mickecamino/RT-datorn/Gamla RT-datorn/CÅ-8001/README-EN.md

# CA-8001 ACIA with 2 serial ports
Apdated schematic för CÅ-8001 - the ones in the magazine and in the book are unfortunately incorrect.
