mickecamino/RT-datorn/Program från MPU-laren/1982 - 1/README.md

# Program från MPU-laren #1-1982	
```
CLOCKSET.ASM - Program som sätter tiden på en MSM5832
DIR.ASM      - Bra version av DIR som visar mer än standard DIR
FLEXPAT.ASM  - Patch för FLEX 2.65 läs av MSM5832 klocka
UNDEL.ASM    - Återskapar raderade filer
VOXMEM.ASM   - Program som talar - kräver VS-1 Speaker Board
VOXMEM1.ASM  - Program som talar - kräver VS-1 Speaker Board - alternativ röst
```
