mickecamino/RT-datorn/Gamla RT-datorn/CÅ-8010/README-EN.md

# CA-8010 EPROM-programmer
EPROM-programmer for RT-computer  
A programmer that programs 2708, 2716 with three different voltages, 2716/2516 with single voltage and 2532/2732.

## Files
* CPROG.CMD  -  CÅ-Elektronik Epromprogrammer Cprog 1.0 for 6809
* TPROG.CMD  -  CÅ-Elektronik Epromprogrammer Tprog 1.0 for 6808
* CÅ-8010 manual.pdf - Manual for the programmer
