mickecamino/RT-datorn/Gamla RT-datorn/CÅ-6819/README-EN.md

# CA-6819 CPU board
CPU board with two processorns, 6800 and 6809, selectable with a switch.  

Monitors:
6800 - TBUG 2C
```
TBUG-2C-E400.bin
TBUG-2C-EC00.bin
```
6809 - CBUG 2.3
```
CBUG-2.3-F800.bin
CBUG-2.3-FC00.bin
```
