mickecamino/RT-datorn/Nya RT-datorn/RT-Backplane/README-EN.md

# Backplane for RT-datorn.
A backplane for RT-datorn with 8 slots and a Phoenix-plug for power and connector for External Reset.
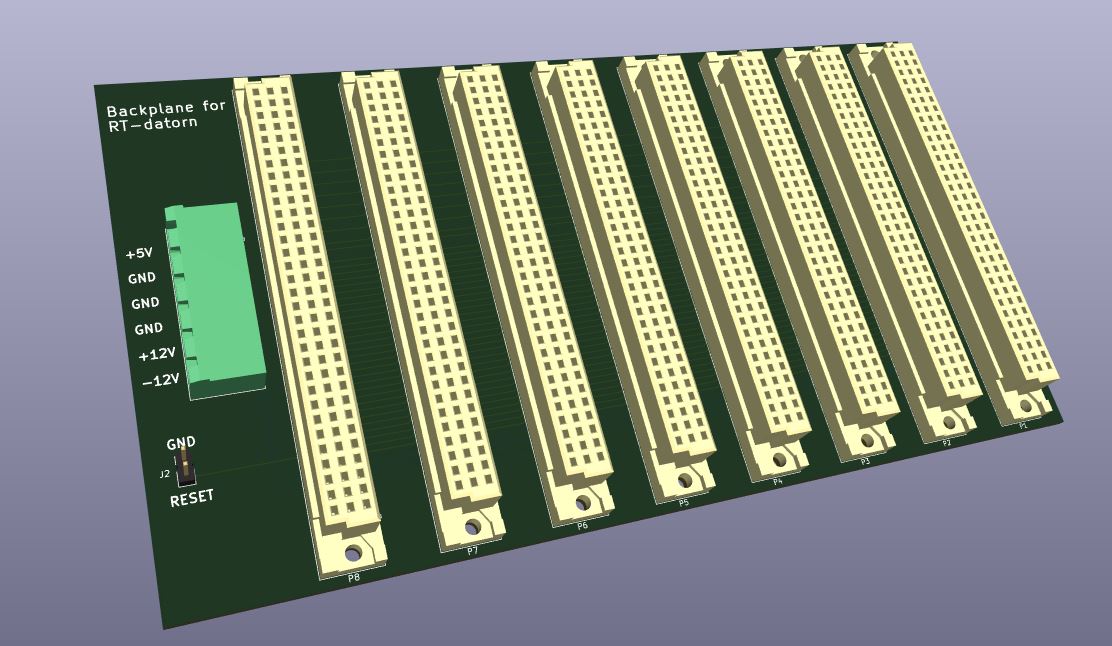
[picture p1: Nya RT-datorn/RT-Backplane/RT-backplane.jpg]
RT-Backplane
