mickecamino/RT-datorn/Nya RT-datorn/RT-Backplane/README.md

# Bakplan för RT-datorn.
Ett backplan för RT-datorn med 8 slottar och en Phoenix-plug för spänningsmatning samt uttag för External Reset.
RT-Backplane
