mickecamino/RT-datorn/Gamla RT-datorn/CÅ-800/README-EN.md

# CA-800 Motherboard
The first version of the motherboard, repalced with CA-801.  
The difference is that the power supply parts are moved off the motherboard and some component changes were made.
