mickecamino/RT-datorn/Gamla RT-datorn/CÅ-8014/README-EN.md

# CA-8014 Centronics printer output
Peripheral board with Centronics output for connecting parallel printers.  
No documentation or schematic found.
