mickecamino/RT-datorn/Gamla RT-datorn/CÅ-8015/README-EN.md

## CA-8015 - Real Time Clock
This peripheral board, with MSM5832, is a newer Real time Clock than CA-8005.  
The clock chip is a "real" real time clock used for computers with proper address and data ports.
