mickecamino/RT-datorn/Gamla RT-datorn/CÅ-8016/README-EN.md

# CA-8016 - Sound Effect board with SN76477
This peripheral board was probably never made due to low interest accoring to an article in the member magazine MPU-laren.  
It was listed in an old price list from Telko.
