mickecamino/RT-datorn/Gamla RT-datorn/CÅ-8017/README-EN.md

# CA-8017 - Floppy Controller
Peripheral board for connecting up to four single or double sided floppy drives, single density only.  
The peripheral board exists in two versions, CA-8017 and CA-8017B. The B variant fully supports double sided floppy drives
.
