mickecamino/RT-datorn/Gamla RT-datorn/CÅ-8018/README-EN.md

# CA-8018 - IEEE-488-bus connection
A special peripheral board for connecting IEEE-488 units.  
Also called HP-IP or GBIP. Used for controlling and reading instruments.
