mickecamino/RT-datorn/Gamla RT-datorn/CÅ-8020/README-EN.md

# CA-8020 - DEBUG board
For debugging the RT-computer.  
No documentation or schematic found.
