mickecamino/RT-datorn/Gamla RT-datorn/CÅ-8025/README-EN.md

# CA-8025 - EPROM board
EPROM board for 8 pcs. 2K 2516 EPROMS. Up to three cards can be used in the RT-computer.
