mickecamino/RT-datorn/Gamla RT-datorn/CÅ-8027/README-EN.md

## CA-8027 - Arithmetic Processing Unit
This board with AM9511 havean Arithmetic Processing Unit (APU) device that provides high performance fixed and floating point arithmetic and a variety of floating point
trigonometric and mathematical operations, 16 and 32 bits fixed point operations and 32 bits floating point operations.  

No program examples found for this board.
