mickecamino/RT-datorn/Gamla RT-datorn/CÅ-8030/README-EN.md

## CA-8030 - Unknown function
This board was donated by Åke Holm. No silk screen or documantation exists.  
The only bus connection used are +5v, +12v, -12v, R/W, D0, RESET, A0, A1 and GND
