mickecamino/RT-datorn/Gamla RT-datorn/CÅ-8034/README-EN.md

## CA-8034 - Unknown function
This board was donated by Åke Holm. No silk screen or documentation exists.  
The board uses all bus connectors and has a 12-pin connector at the top.  
The board seems to be using one 74LS138 and two 6821 PIA
