mickecamino/RT-datorn/Gamla RT-datorn/CÅ-8091/README-EN.md

# CA-8091 - Lab board with PIA
Lab board with 6821 PIA.
