mickecamino/RT-datorn/Gamla RT-datorn/CÅ-8092/README-EN.md

# CA-8092 - Lab board ACIA/SSDA/ADLC
Lab board with ACIA (Asynchronous Communications Interface Adapter), SSDA (Synchronous Serial Data Adapter) and ADLC (Advanced Data Link Controller)
