mickecamino/RT-datorn/Gamla RT-datorn/CÅ-8095/README-EN.md

# CA-8095 - Riser board for the 22-pin bus
A riser board for the 22-pin peripheral bus. Used for testing and fault finding on peripheral cards.
