mickecamino/RT-datorn/Gamla RT-datorn/CÅ-9000/README-EN.md

# CA-9000 - Riser board for the CPU-card
A riser board for the CPU card. Used for test and fault finding.
