mickecamino/RT-datorn/Nya RT-datorn/CÅ-813/README-EN.md

# CÅ-813 I/O board with RTC	
The new board for serial communication is called CÅ-813 and it replaces the older boards 8001, 8014 and 8015.  
It features a programmable serial communication IC for V24, a printer connection with parallel interface (Centronics) and a Real Time Clock (MSM5832) with battery backup.  
The connection for printer and serial is via a 60-pin connector. 36 pins for the printer and 24 for the serial interface.  
At least two releases were made:
CÅ-813, first release with an INS2651 as ACIA.  
CÅ-813A, second release with a 6551 as ACIA.  

See also CÅ-833
