mickecamino/RT-datorn/Nya RT-datorn/CÅ-816/README-EN.md

# CÅ-816 - EPROM board
The new EPROM-board is called 816 and has 16 EPROM-sockets for 2532 EPROM's, each EPROM contains 4 kb. A total of 64 kb permanent memory is possible.. 
The board can hold for, example, the operating system FLEX and a BASIC interpreter. The addressing of the EPROM board is done via one single address. With a small software routine, loading from the boards EPROM to computer RAM is really simple.  CBUG 4.3 also has a loader routine for loading a special version of FLEX, no info so far about this FLEX version is found.  
The board replaces the 8025-board.  

Se also CÅ-836
