mickecamino/RT-datorn/Nya RT-datorn/CÅ-817/README-EN.md

# CÅ-817 - Diskett-interface
The driver IC's for floppy drives on board 817 is equal to the board 8017. Up to four floppy drives, either single or double sided, single density can be connected.  
No info or schematic is found for this board.  

See also CÅ-837.
