mickecamino/RT-datorn/Nya RT-datorn/CÅ-831/README-EN.md

# CÅ-831 - Terminal board - simple
The simple hexadecimal terminal 8006 is replaced by 831, almost identical except that 831 also have a PIA for lab use.  
  
No info or schematic found for this board (yet)
