mickecamino/RT-datorn/Nya RT-datorn/CÅ-834/README-EN.md

# CÅ-834 - memory board for static RAM chips
New memory board for static memory, 6116 2k or EPROM 2716. Replaces CÅ-814.  

Schematic was made by reverese engineering the PCB.
