mickecamino/RT-datorn/Nya RT-datorn/CÅ-837/README-EN.md

# CÅ-837 Floppy Controller
A newer Floppy Controller using the WD2792 IC, support for up to four Floppy drives, Single ocr Double Sides, Single or Double Density.  
Schematic was made by reverse engineering the PCB and compare it with a schematic for the "old" RT-computer.
