mickecamino/RT-datorn/Gamla RT-datorn/CÅ-8030/README.md

## CÅ-8030 - Okänd funktion
Detta kort donerades av Åke Holm. Inget komponenttryck eller dokumentation finns.  
De enda busskontakter som finns är +5v, +12v, -12v, R/W, D0, RESET, A0, A1 samt GND
