mickecamino/RT-datorn/Nya RT-datorn/CÅ-815/Schema/README.md

# CÅ-815 - Videoterminal-kort
Schema skapat i KiCad 7.06
