mickecamino/RT-datorn/Nya RT-datorn/CÅ-834/CÅ-834-schema/README.md

# CÅ-834 - minneskort för Statiska RAM-kretsar och/eller EPROM.
Schema skapa i KiCad 7.06
