mickecamino/RT-datorn/Gamla RT-datorn/CÅ-8025/Schema/README.md

# CÅ-8025 - EPROM-kort
Schema skapat i KiCad 7.06
