mickecamino/RT-datorn/Gamla RT-datorn/CÅ-8027/Schema/README.md

## CÅ-8027 - ARITMETIKPROCESSOR
Schema i Kicad 7.06
