mickecamino/RT-datorn/Gamla RT-datorn/CÅ-8008/Schema/README.md

# CÅ-8008 - Analog-digitalomvandlare
Schema skapat i KiCad 7.06
