mickecamino/RT-datorn/Nya RT-datorn/CÅ-814/README.md

# CÅ-814A Minnes-kort
Minneskortet 814 ersätter 6848. 
Det är helt identiskt med undantag av att "refreshen" för de dynamiska minneskretsarna sker kontinuerligt i ställer för som tidigare med 32 kHz. Minneskortet är på 48 kb.  
 
Se även CÅ-834
