mickecamino/RT-datorn/Nya RT-datorn/CÅ-815/README.md

# CÅ-815 - Videoterminal-kort
Terminalkortet är en helt ny konstruktion. Det är en s.k. minnesmappad terminal med 24 rader om vardera 80 tecken. På kortet finns en CRT-kontrollkrets (Motorola MC6845), bildminne samt en PIA för anslutning av tangentbord över en 26-polig kontakt. Den har samma koppling som i byggboken beskrivna terminalen. Bildminnet ligger mellan $E800 och $EFFF och processorn på CÅ-812 tar hand om terminalfunktionerna. All teckenhantering mellan "dator"- och "terminaldel" sker utan inblandning av seriekommunikationskretsar. Förloppet är därför givetvis mycket snabbare än tidigare. Terminalens teckenuppsättning är svensk.
