mickecamino/RT-datorn/Gamla RT-datorn/CÅ-8005/CÅ-8005-schema-RT.jpg

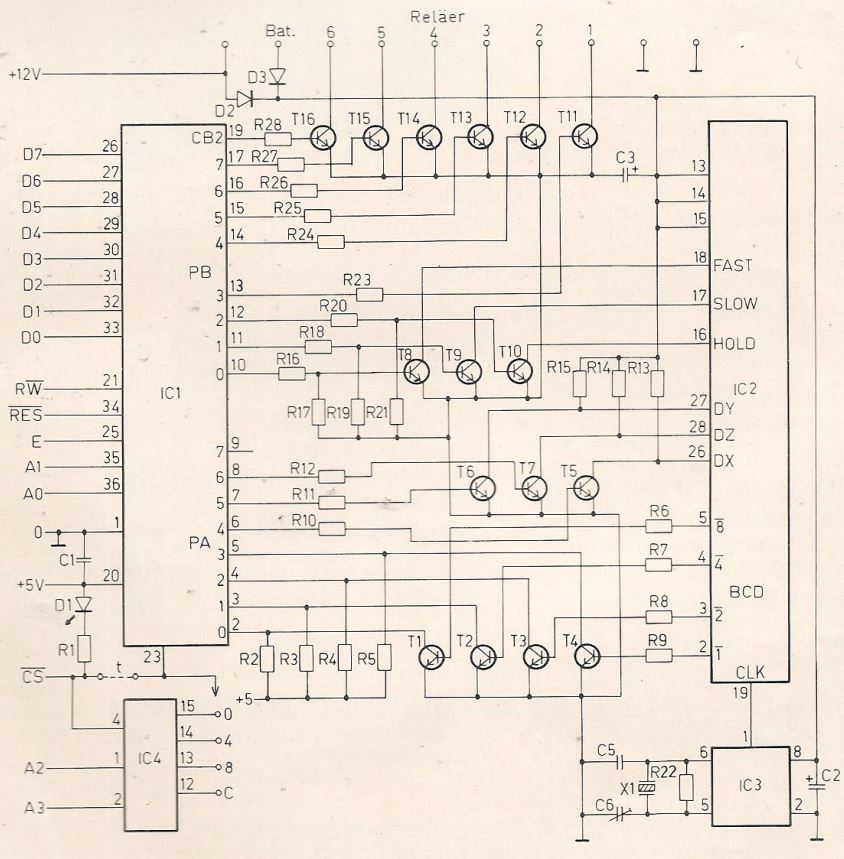
Gamla RT-datorn/CÅ-8005/CÅ-8005-schema-RT.jpg
