mickecamino/RT-datorn/Gamla RT-datorn/CÅ-8005/MM5318-pins.jpg

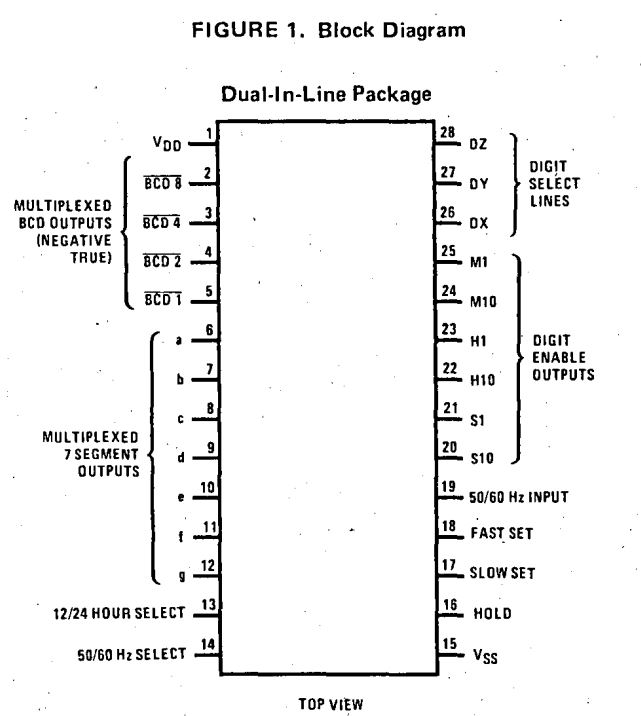
Gamla RT-datorn/CÅ-8005/MM5318-pins.jpg
