mickecamino/RT-datorn/Gamla RT-datorn/CÅ-8027/CÅ-8027.jpg

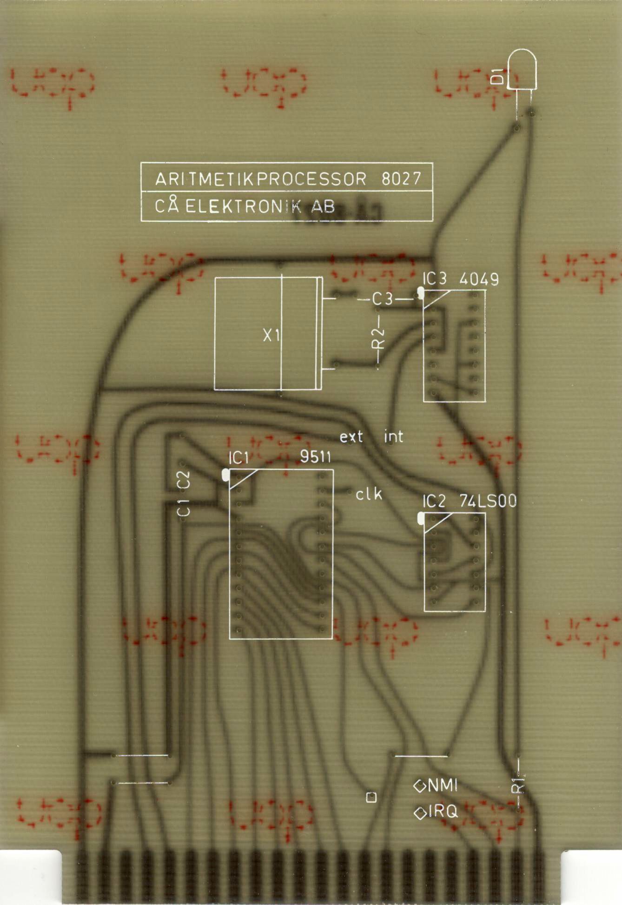
Gamla RT-datorn/CÅ-8027/CÅ-8027.jpg
