mickecamino/RT-datorn/Gamla RT-datorn/CÅ-8030/CÅ-8030-framsida.jpg

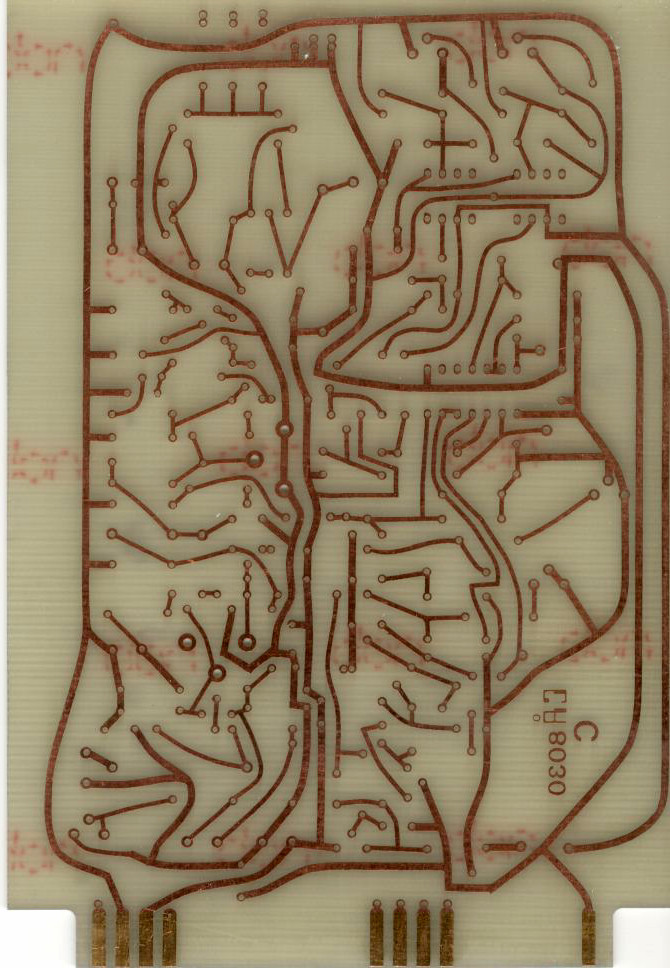
Gamla RT-datorn/CÅ-8030/CÅ-8030-framsida.jpg
