mickecamino/RT-datorn/Gamla RT-datorn/CÅ-8034/CÅ-8034-baksida.jpg

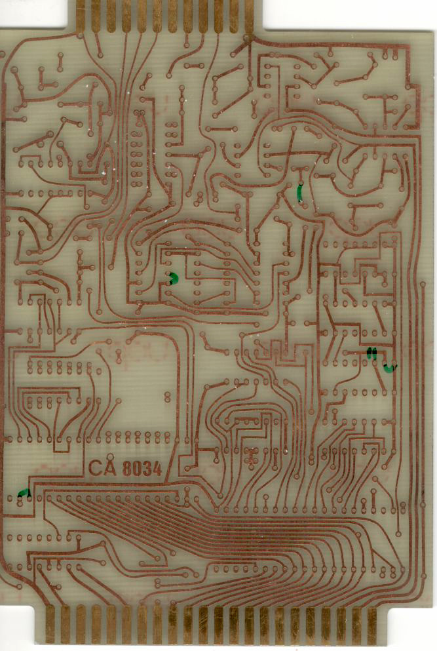
Gamla RT-datorn/CÅ-8034/CÅ-8034-baksida.jpg
