mickecamino/RT-datorn/Gamla RT-datorn/CÅ-8034/CÅ-8034-framsida.jpg

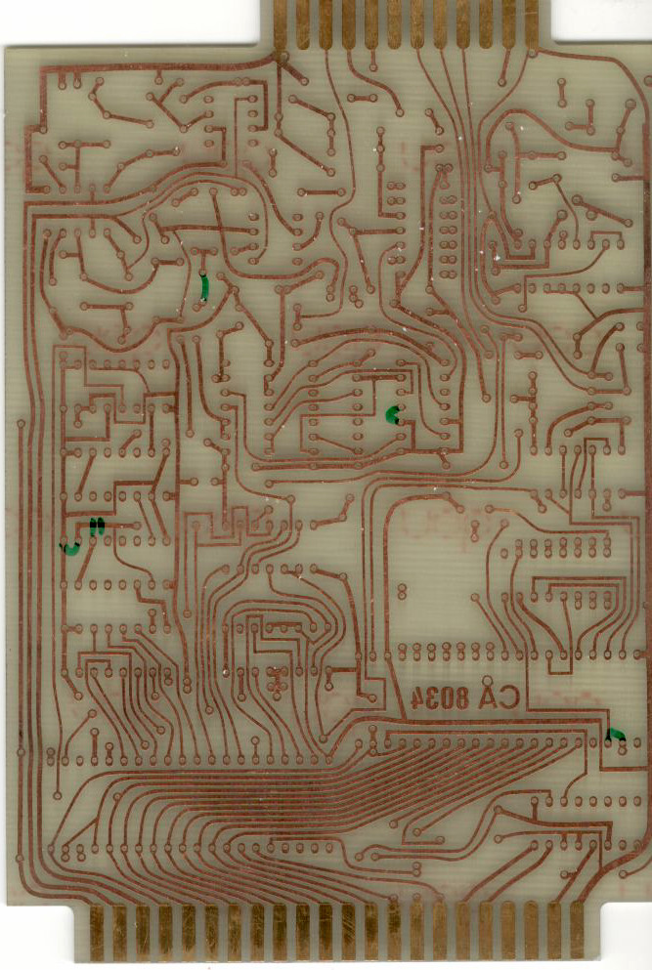
Gamla RT-datorn/CÅ-8034/CÅ-8034-framsida.jpg
