mickecamino/RT-datorn/Nya RT-datorn/CÅ-812/CÅ-812-bestyckat.jpg

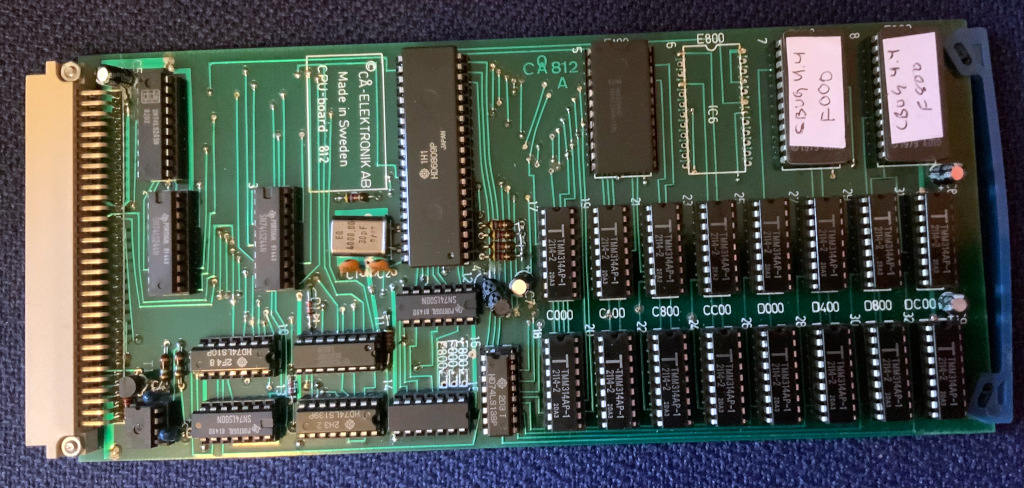
Nya RT-datorn/CÅ-812/CÅ-812-bestyckat.jpg
