mickecamino/RT-datorn/Nya RT-datorn/CÅ-813/CÅ-813-info.jpg

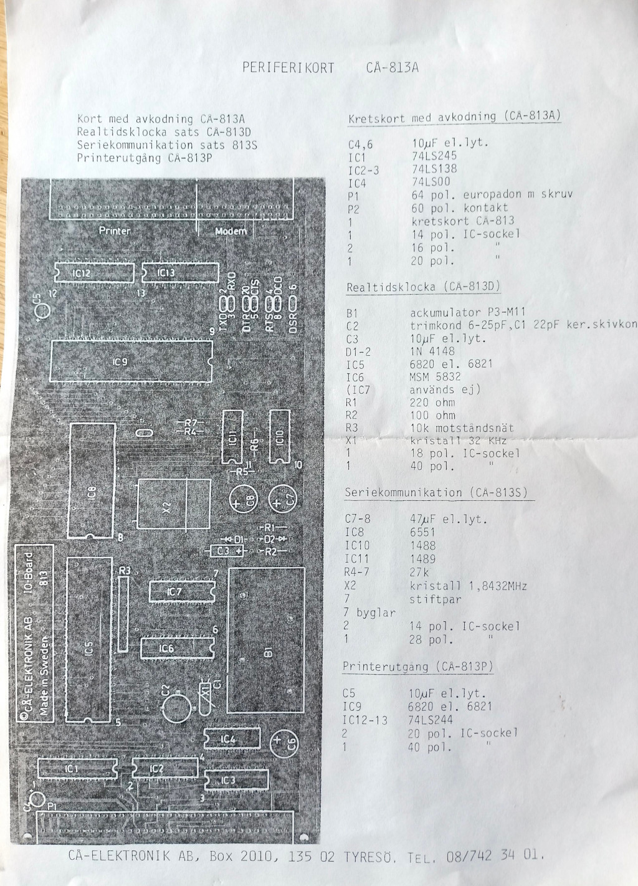
Nya RT-datorn/CÅ-813/CÅ-813-info.jpg
