mickecamino/RT-datorn/Nya RT-datorn/CÅ-813/CÅ-813-pcb-back.jpg

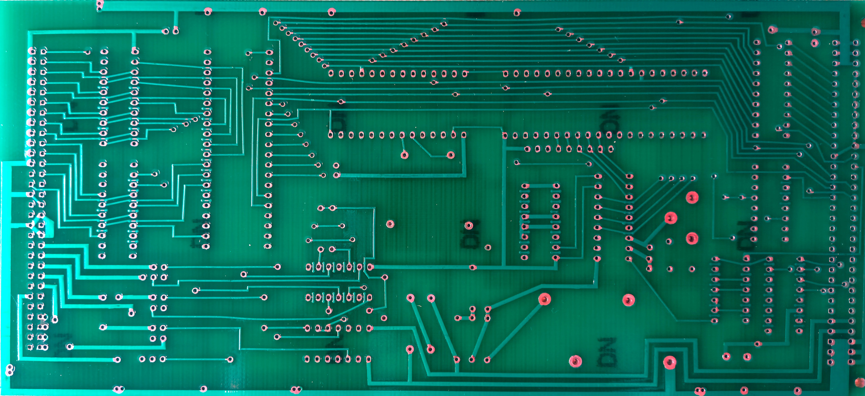
Nya RT-datorn/CÅ-813/CÅ-813-pcb-back.jpg
