mickecamino/RT-datorn/Nya RT-datorn/CÅ-814/CÅ-814-info.jpg

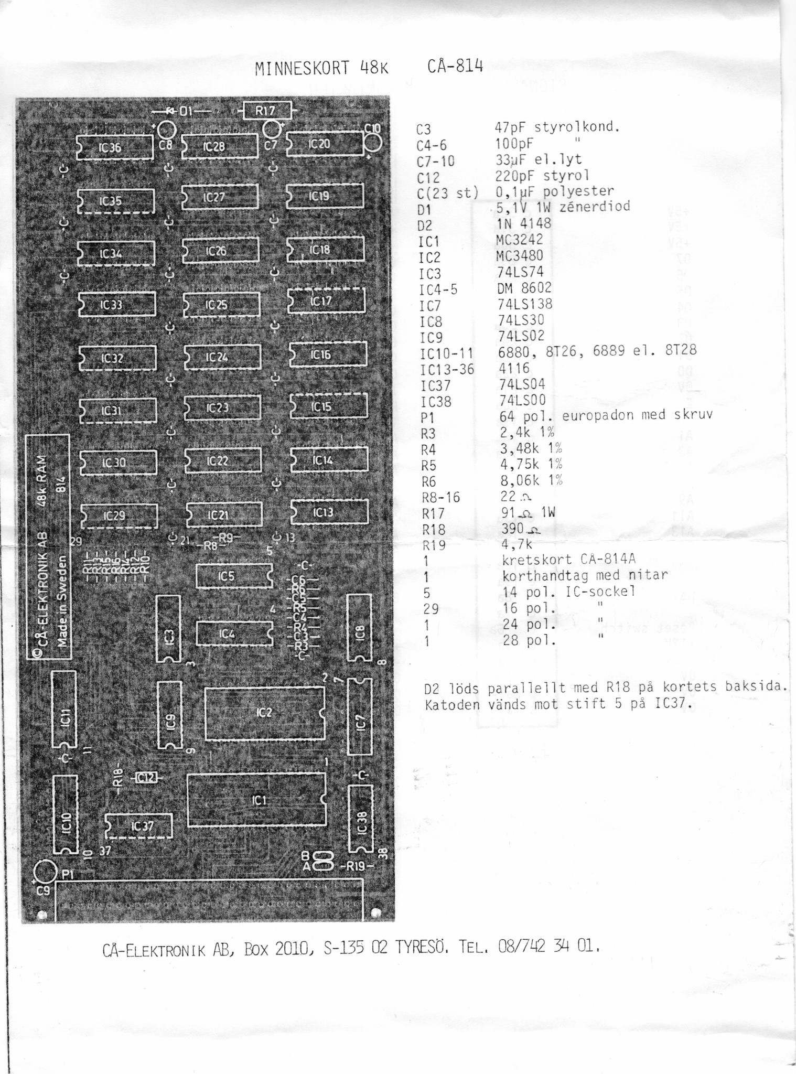
Nya RT-datorn/CÅ-814/CÅ-814-info.jpg
