mickecamino/RT-datorn/Nya RT-datorn/CÅ-815/CÅ-815-info.jpg

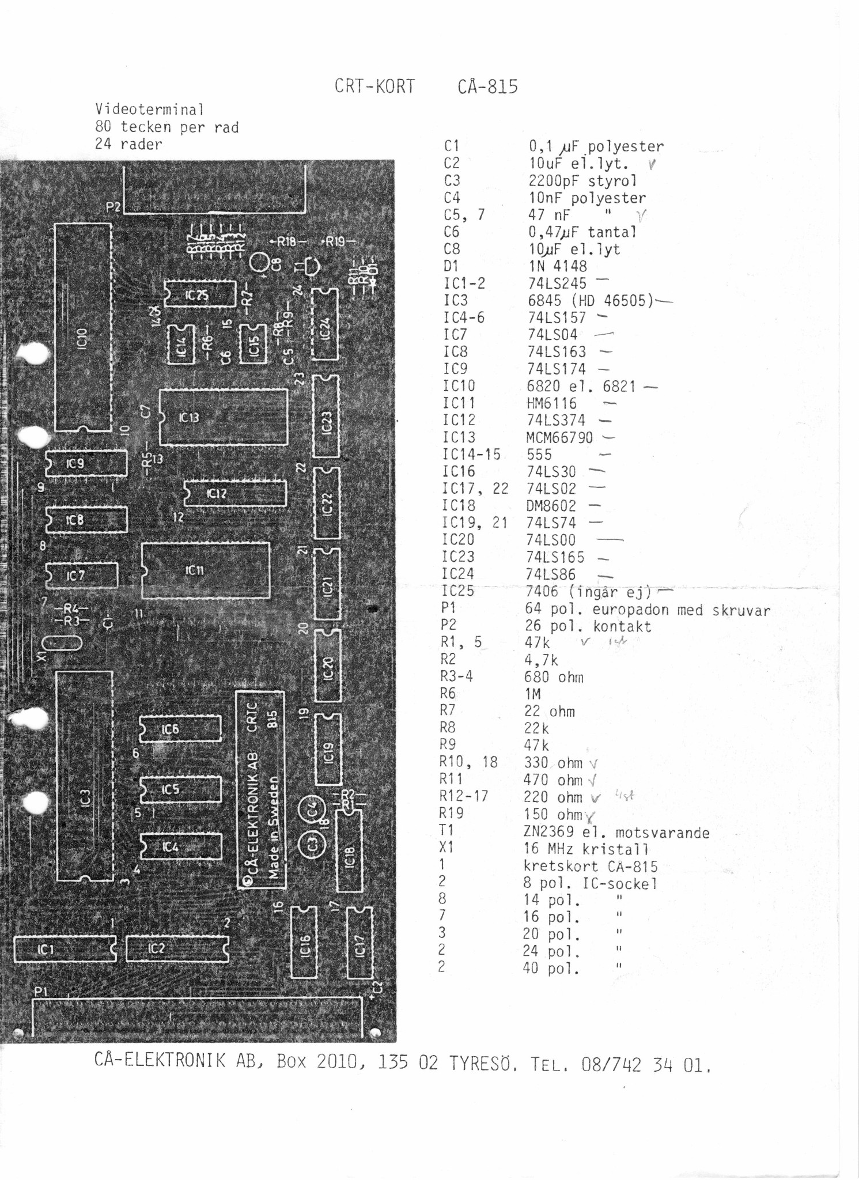
Nya RT-datorn/CÅ-815/CÅ-815-info.jpg
