mickecamino/RT-datorn/Nya RT-datorn/CÅ-816/CÅ-816-info.jpg

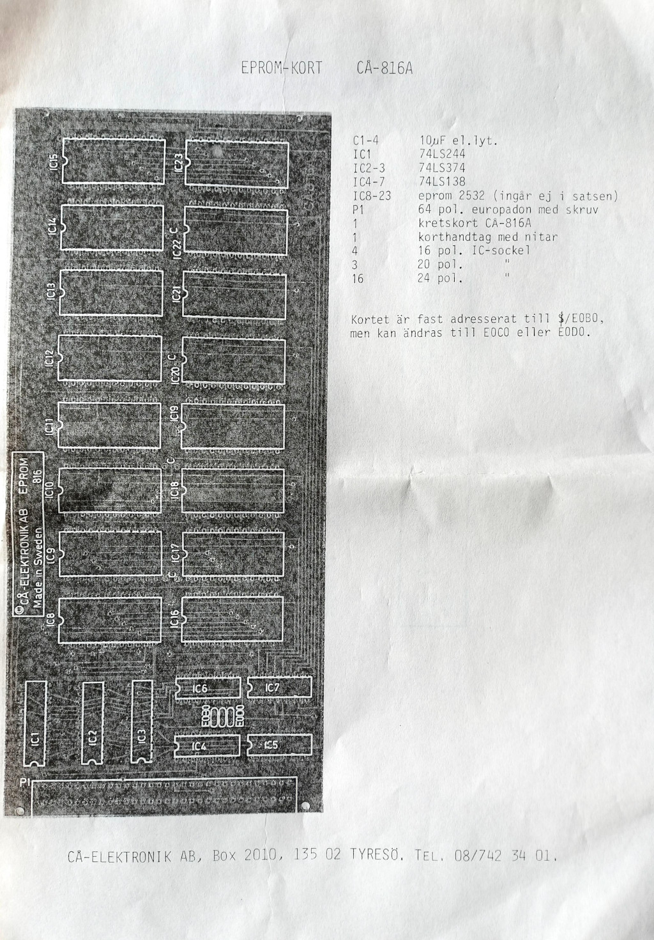
Nya RT-datorn/CÅ-816/CÅ-816-info.jpg
