mickecamino/RT-datorn/Nya RT-datorn/CÅ-816/CÅ-816-pcb-front.jpg

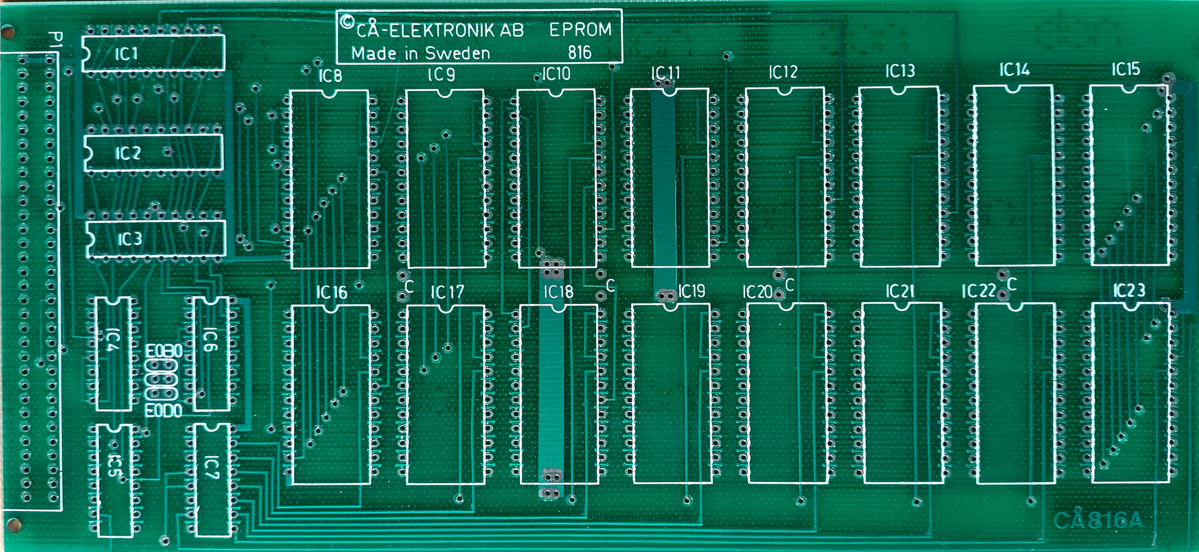
Nya RT-datorn/CÅ-816/CÅ-816-pcb-front.jpg
