mickecamino/RT-datorn/Nya RT-datorn/CÅ-833/CÅ-833-bestyckat.jpg

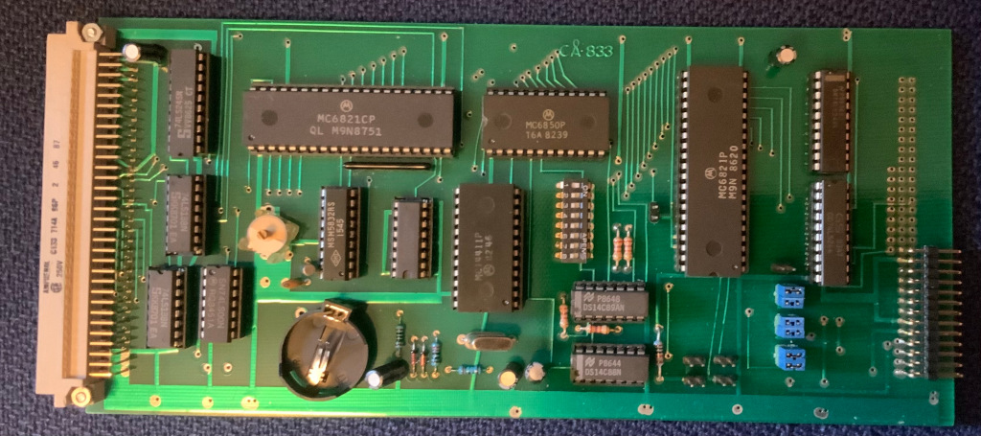
Nya RT-datorn/CÅ-833/CÅ-833-bestyckat.jpg
