mickecamino/RT-datorn/Nya RT-datorn/CÅ-833/CÅ-833.jpg

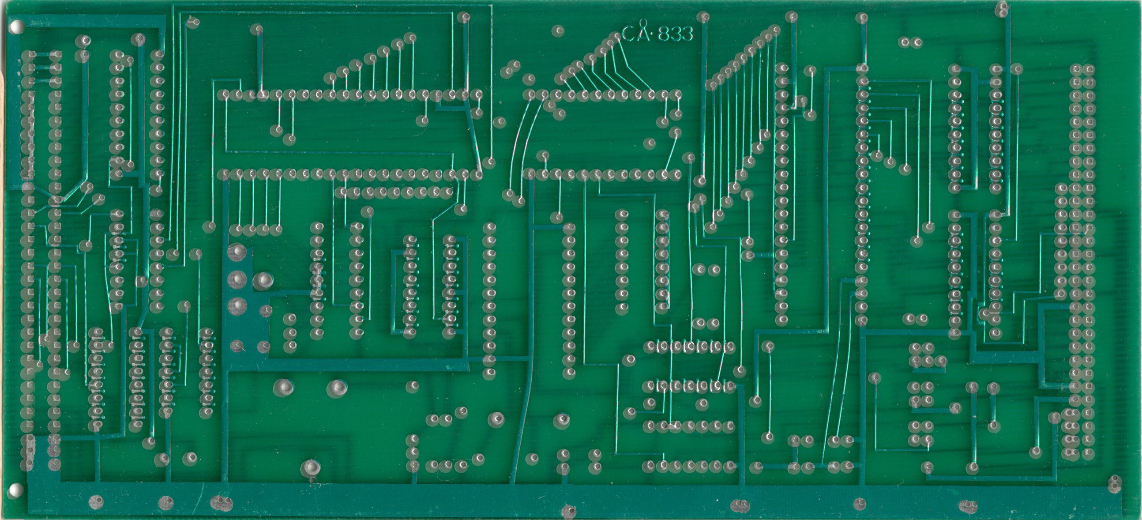
Nya RT-datorn/CÅ-833/CÅ-833.jpg
