mickecamino/RT-datorn/Nya RT-datorn/CÅ-834/CÅ-834.jpg

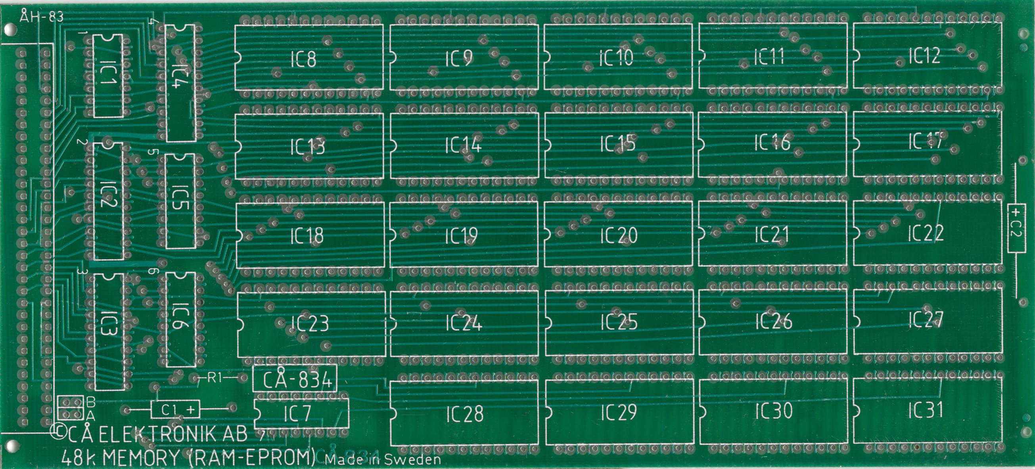
Nya RT-datorn/CÅ-834/CÅ-834.jpg
