mickecamino/RT-datorn/Nya RT-datorn/CÅ-836/CÅ-836-front.jpg

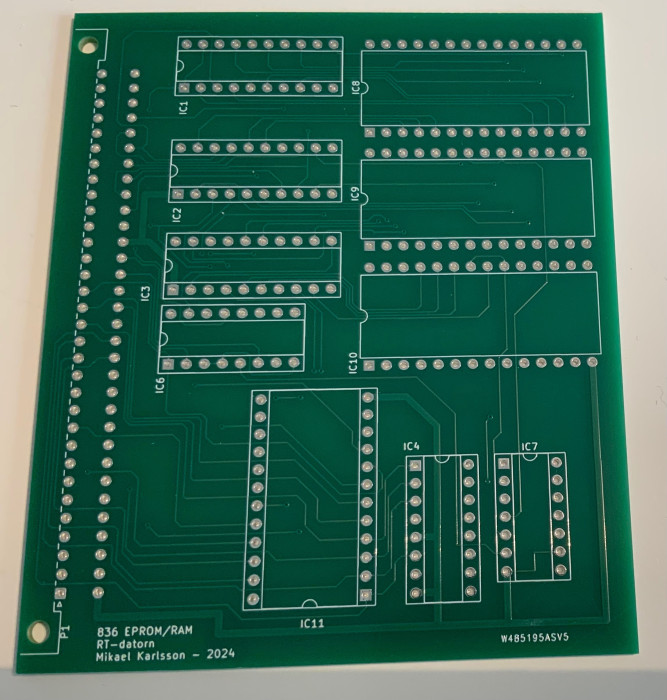
Nya RT-datorn/CÅ-836/CÅ-836-front.jpg
