mickecamino/RT-datorn/Nya RT-datorn/CÅ-837/CÅ-837-bestyckat.jpg

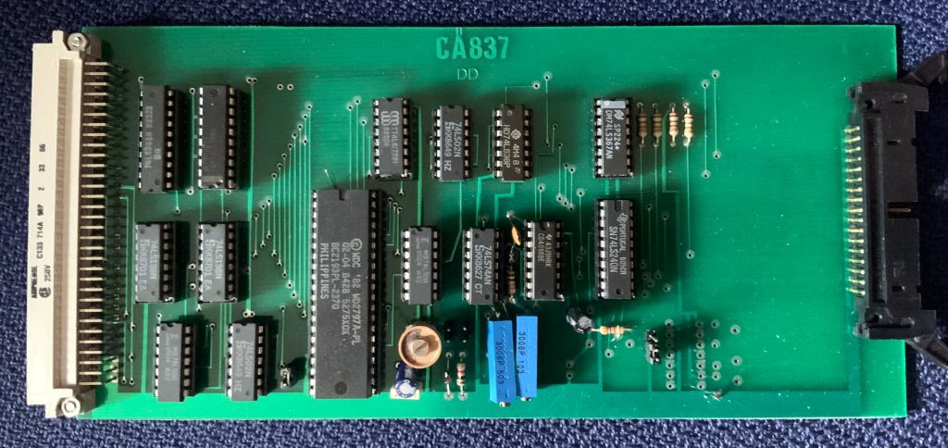
Nya RT-datorn/CÅ-837/CÅ-837-bestyckat.jpg
