mickecamino/RT-datorn/Nya RT-datorn/CÅ-837/CÅ-837.jpg

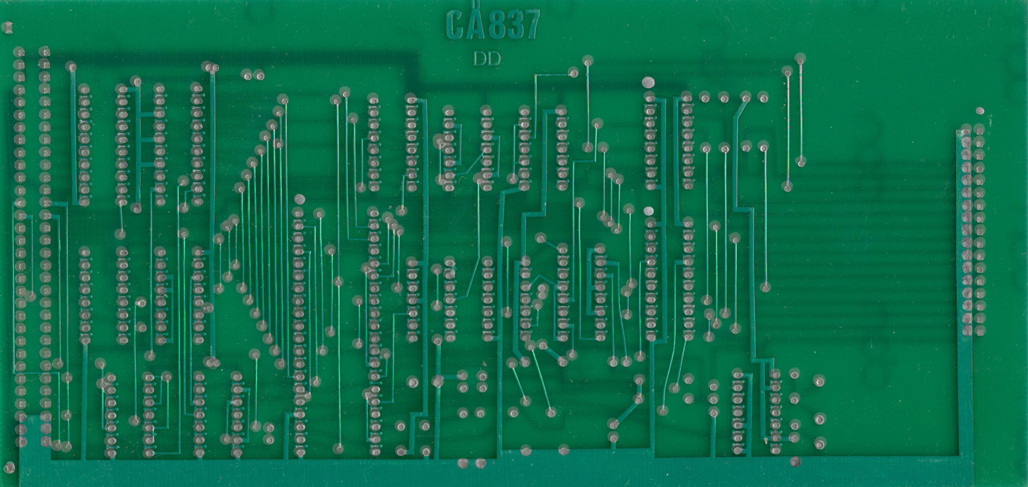
Nya RT-datorn/CÅ-837/CÅ-837.jpg
