mickecamino/RT-datorn/Flex Operating System/Utilities/README-EN.md

# Utilities
## A collection of different FLEX programs
```
DISKIDEN.ASM  -   View a FLEX diskette information, can change volume name and version.
```
Example of output:
```
+++DISKIDEN

Disk Volume Name: FLEX-SWT
Disk Volume Number: 1177
Disk Creation Date: 10/3/80
Disk Format: 35 Tracks, 10 Sectors, 5"
Free Sectors: 110
Free Track/Sectors: First 1B/01, Last 04/04
Change Disk Name or Number(y/n)? N

Diskiden Completed!
+++DISKIDEN 1

Disk Volume Name: BASIC
Disk Volume Number: 1024
Disk Creation Date: 3/8/124
Disk Format: 40 Tracks, 36 Sectors, Double-Sided, Double-Density, 5"
Free Sectors: 497
Free Track/Sectors: First 1A/08, Last 27/24
Change Disk Name or Number(y/n)? N

Diskiden Completed!
```
