mickecamino/RT-datorn/Nya RT-datorn/CÅ-812/CA-812A-schema.pdf

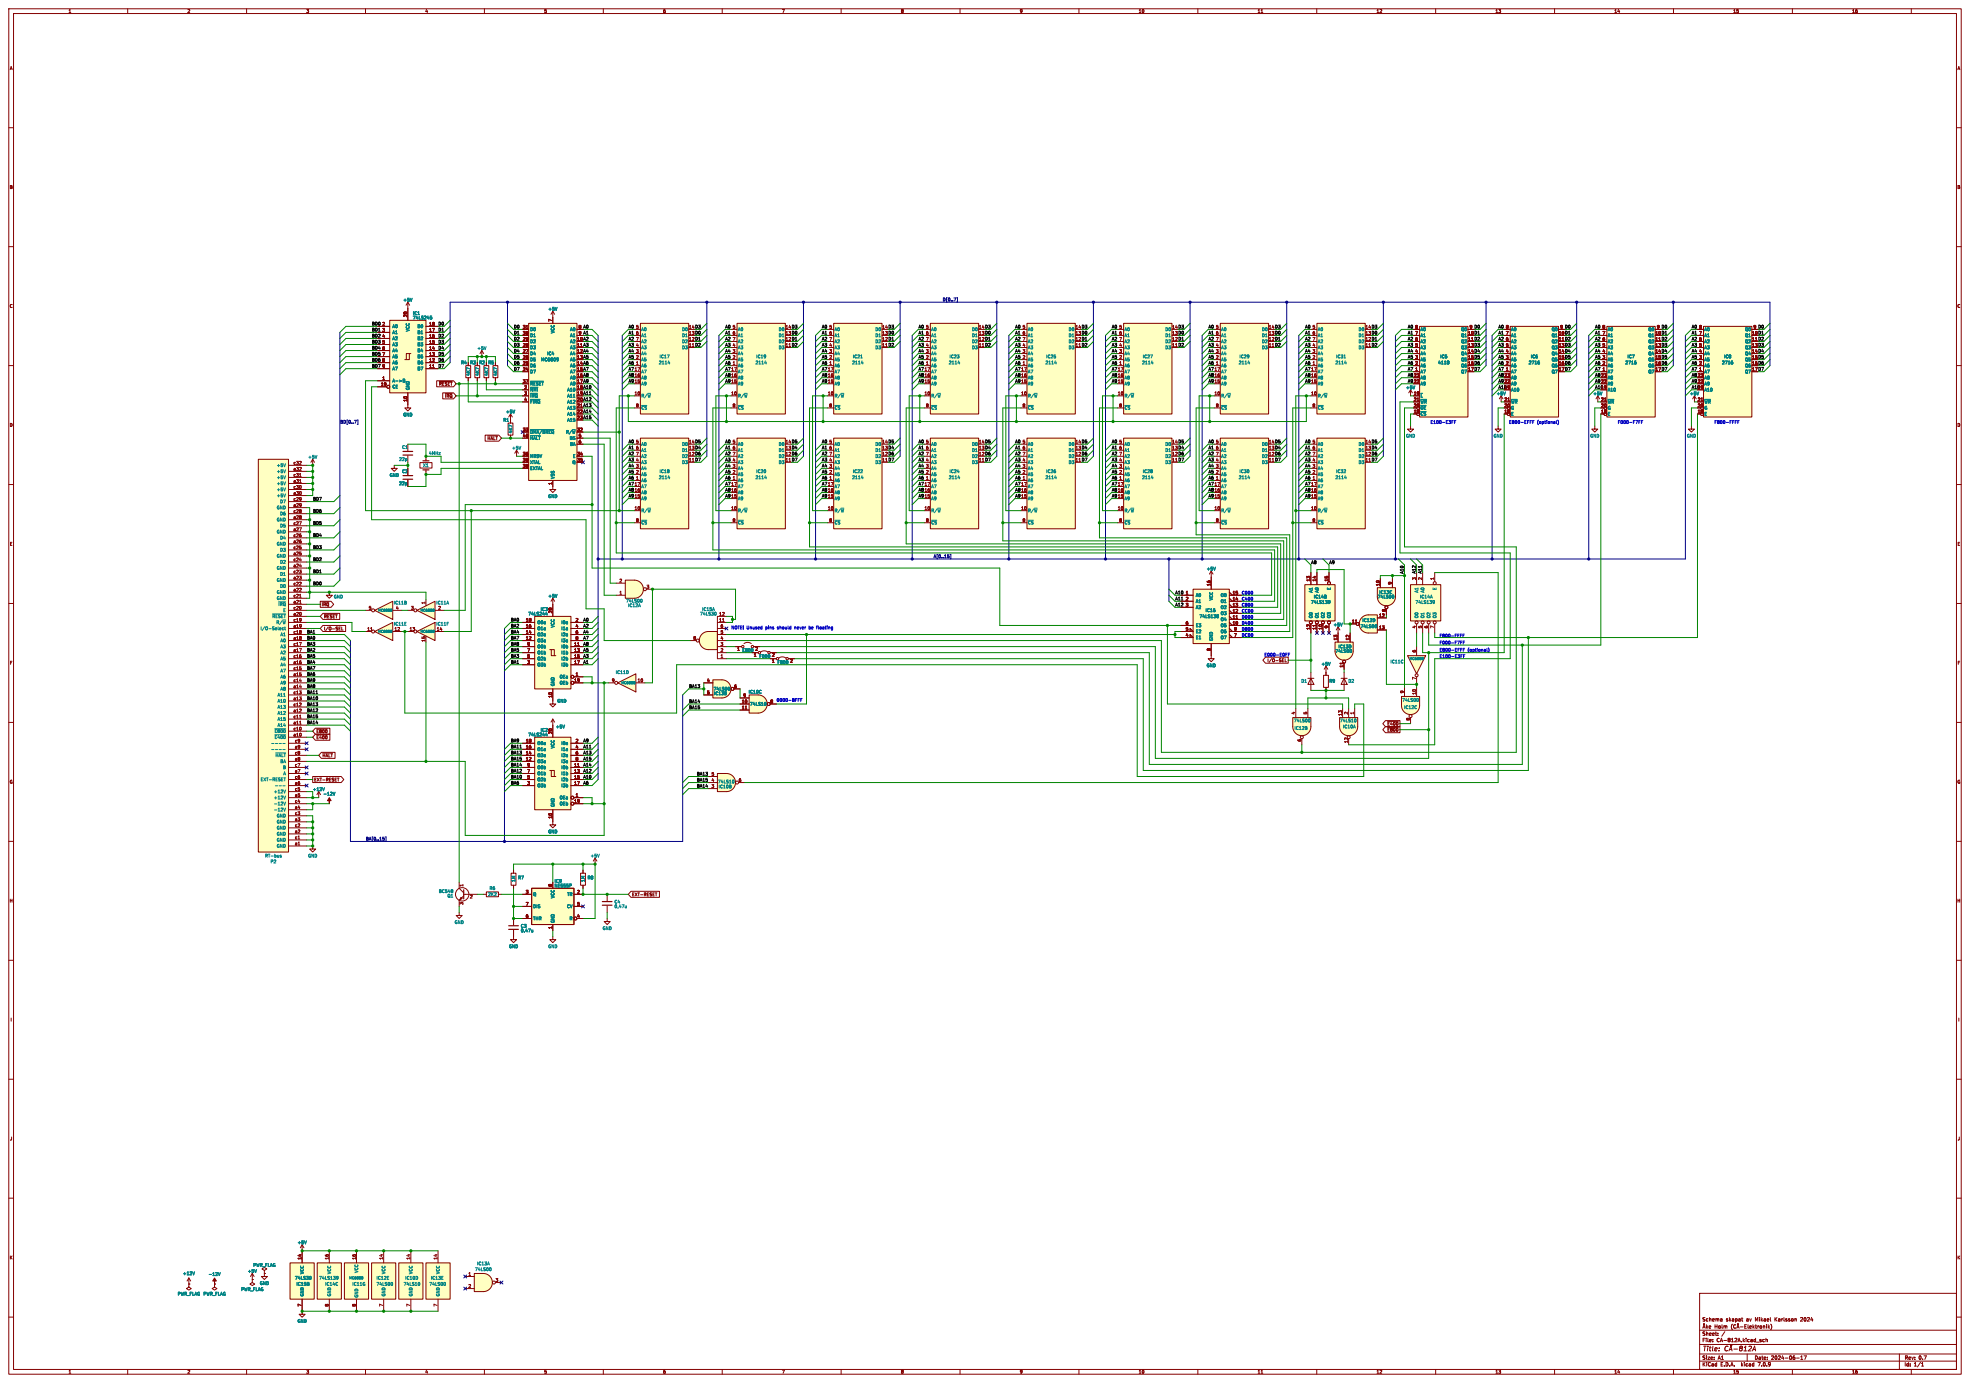
[picture p42: page 1]

1 A2 10 A3 11 A4 12 A5 13 A6 14 A7 15 A8 16 A9 17 A10 18 A11 19 ~{NMI} 2 A12 20 A13 21 A14 22 A15 23 D7 24 D6 25 D5 26 D4 27 D3 28 D2 29 ~{IRQ} 3 D1 30 D0 31 R/~{W}32 ~{DMA/BREQ} 33 E

EXT-RESET
