mickecamino/RT-datorn/Nya RT-datorn/CÅ-813/CÅ-813A-schema.pdf

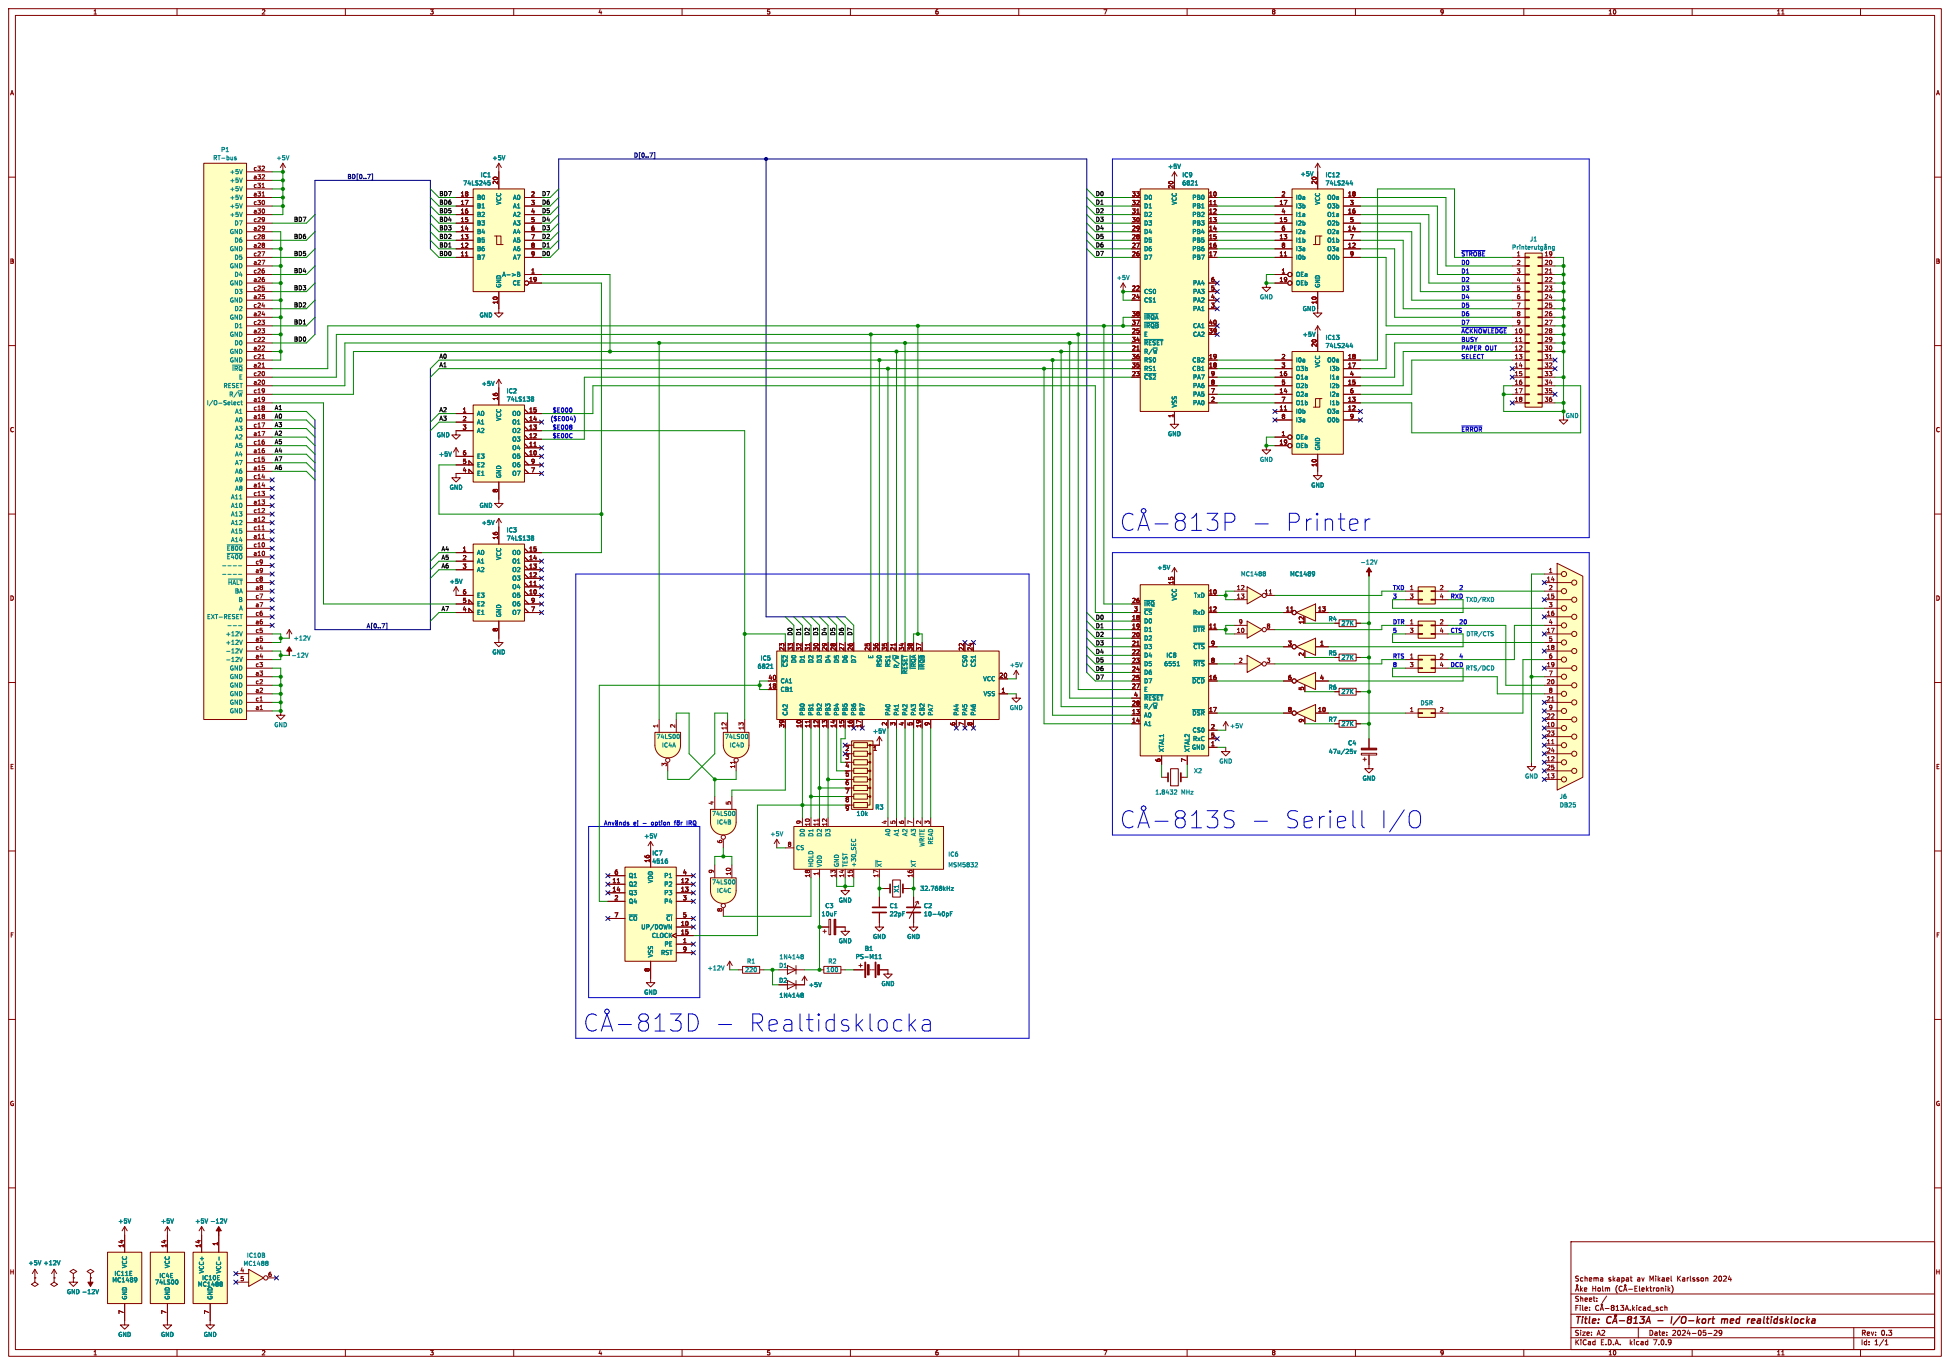
[picture p43: page 1]

~{ACKNOWLEDGE} BUSY þÿCÅ-813D - Realtidsklocka

þÿAnvänds ej - option þÿför IRQ

1 D1 10 D2 11 D3 12 GND 13 TEST 14 +30_SEC 15 XT 16 ~{XT} 17 HOLD 18 WRITE
