mickecamino/RT-datorn/Nya RT-datorn/CÅ-834/CÅ-834-schema.pdf

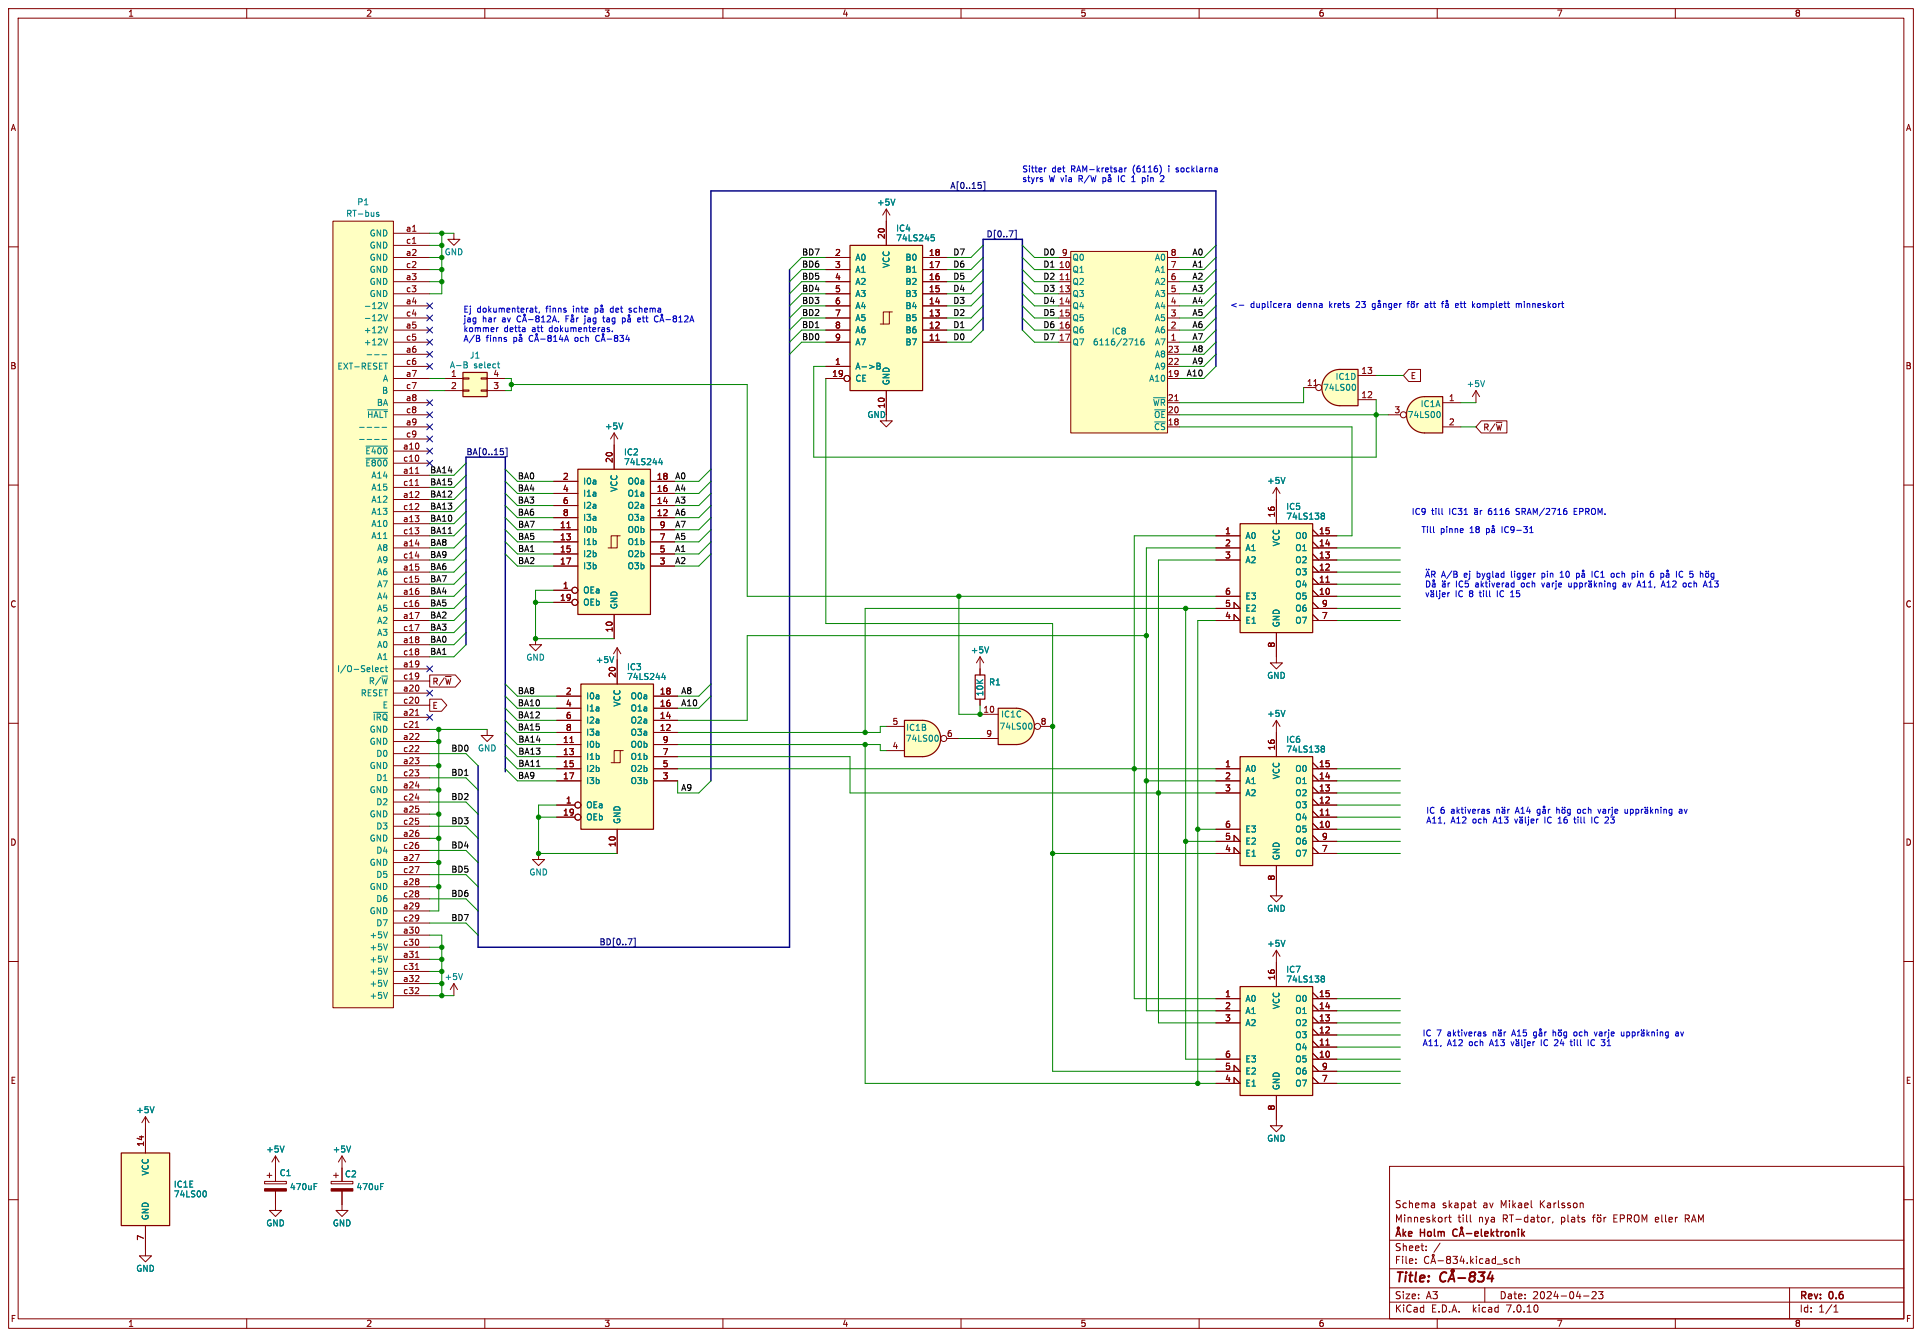
[picture p44: page 1]

jag har av þÿCÅ-812A. þÿFår jag tag þÿpåett þÿCÅ-812A

þÿÄRA/B ej byglad ligger pin 10 þÿpåIC1 och pin 6 þÿpåIC 5 þÿhög
þÿväljer IC 8 till IC 15
