mickecamino/RT-datorn/Nya RT-datorn/CÅ-815/CÅ-815-schema.pdf

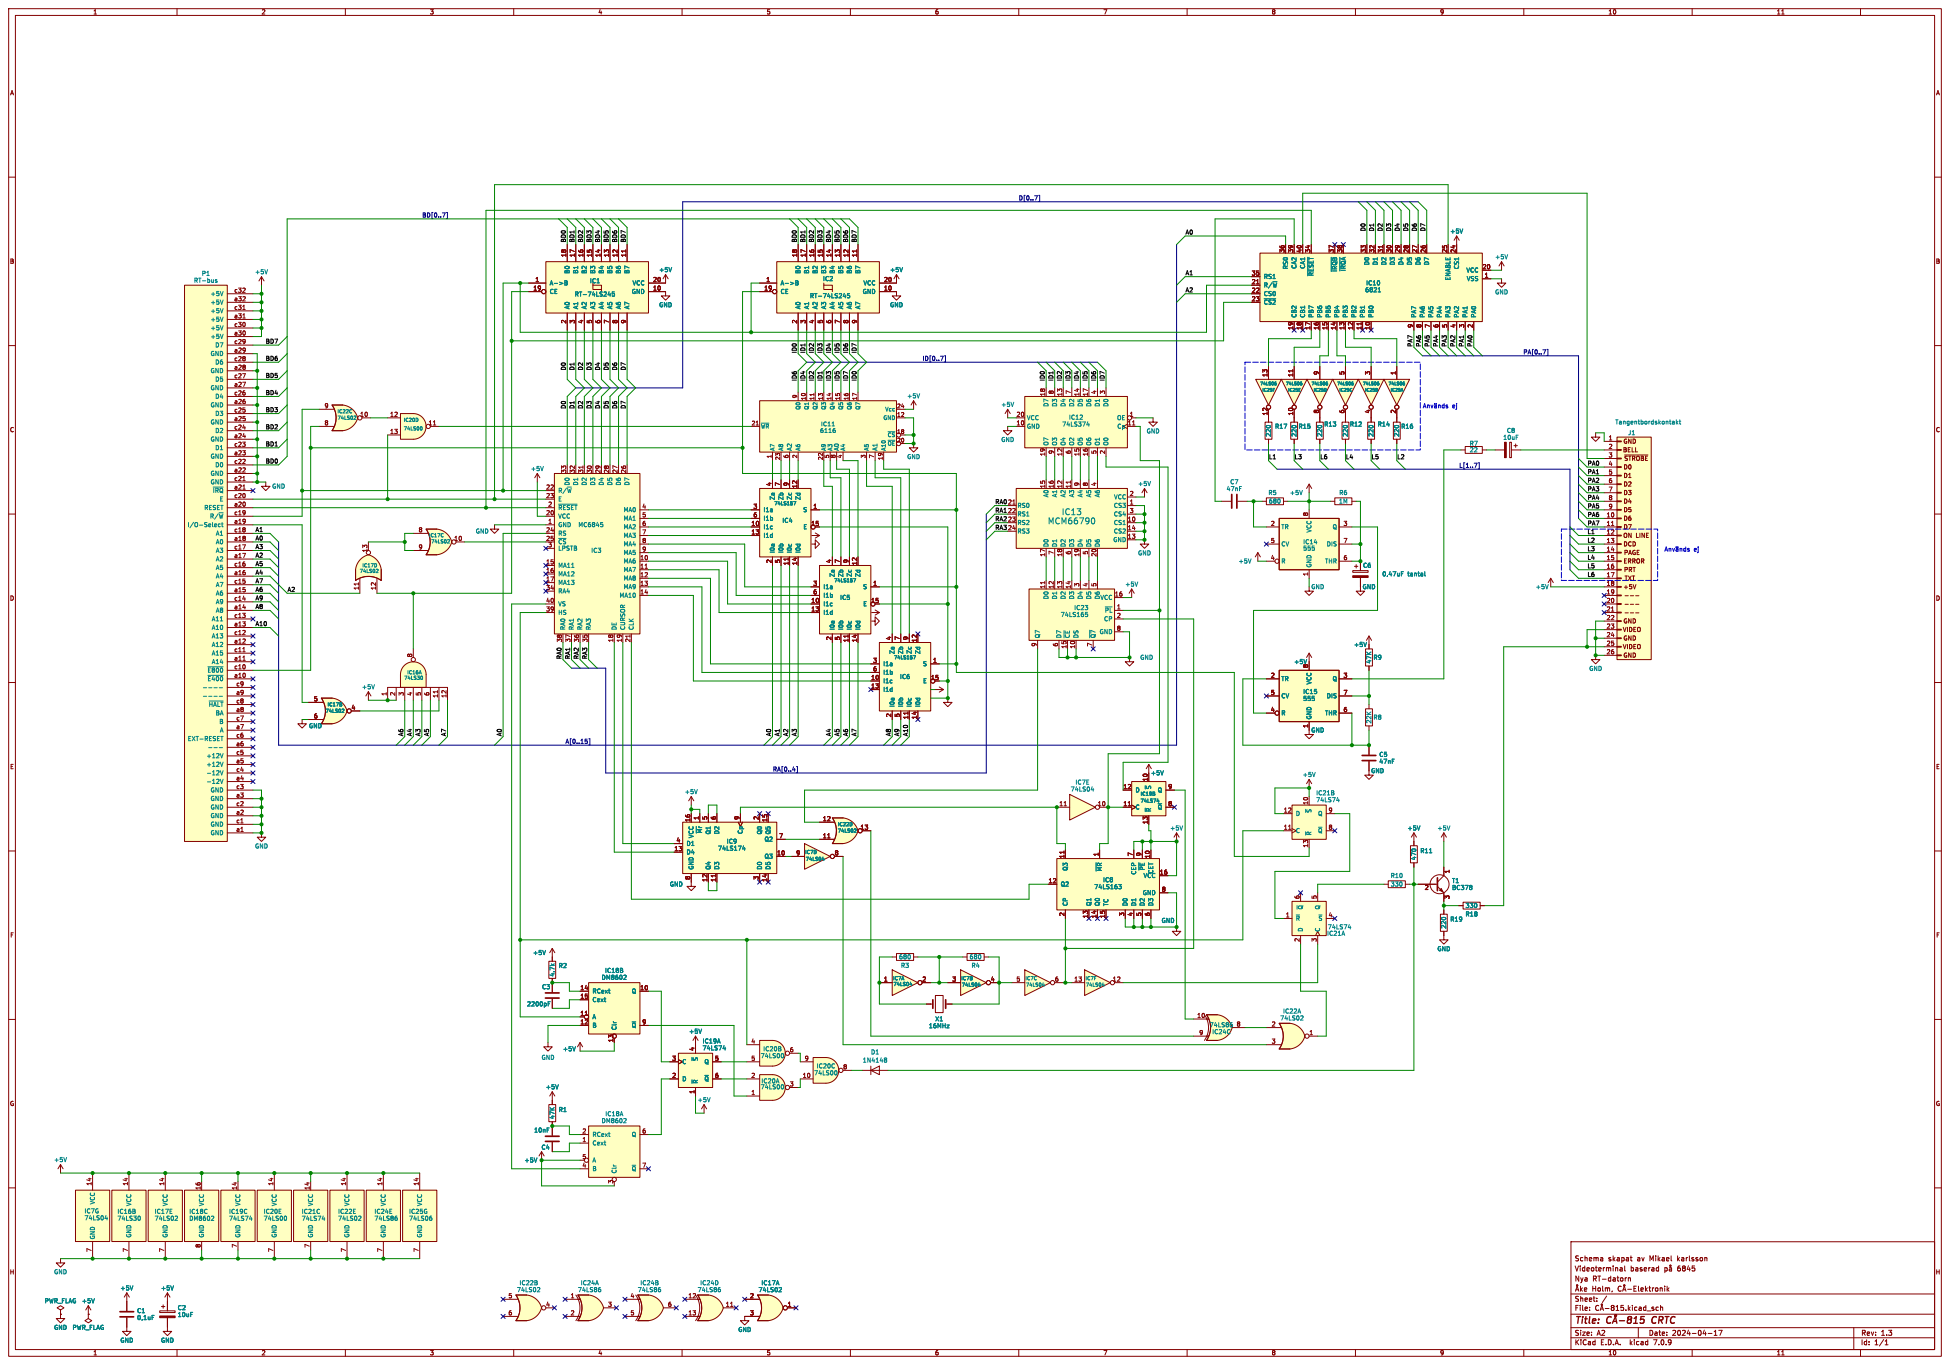
[picture p45: page 1]

File: þÿCÅ-815.kicad_sch Sheet: / þÿÅkeHolm, þÿCÅ-Elektronik
