mickecamino/RT-datorn/Gamla RT-datorn/CÅ-8027/CÅ-8027-schema.pdf

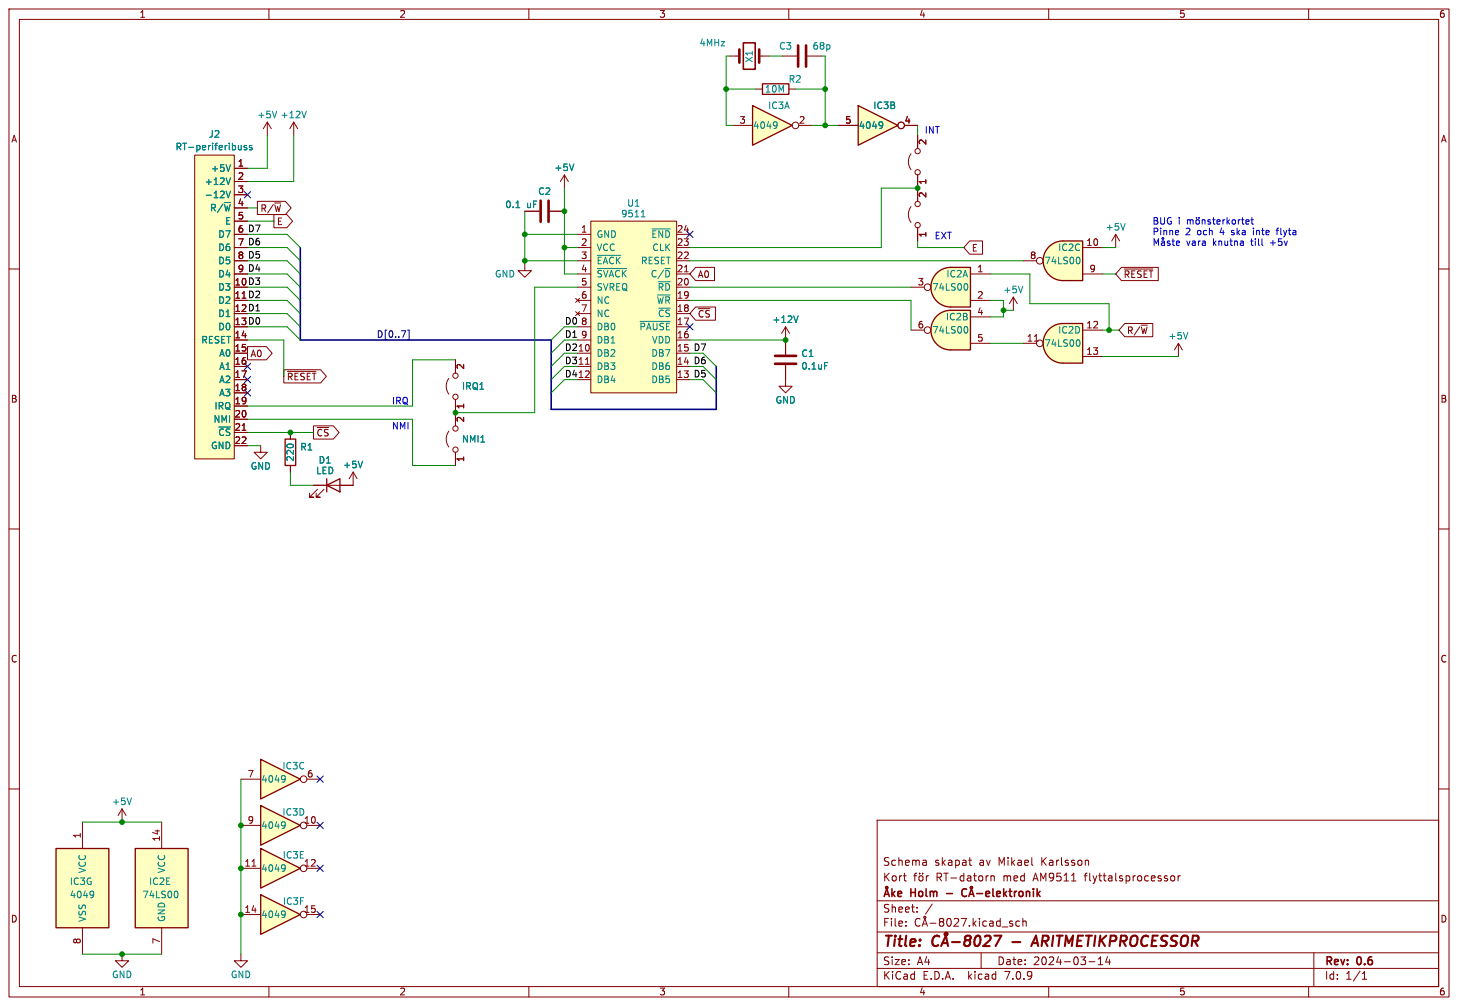
[picture p46: page 1]

BUG i þÿmönsterkortet Pinne 2 och 4 ska inte flyta

IRQ 19 NMI 20 ~{CS} 21 GND 22

Id: 1/1 Title: þÿCÅ-8027 - ARITMETIKPROCESSOR
