mickecamino/RT-datorn/Gamla RT-datorn/CÅ-8025/CÅ-8025-schema.pdf

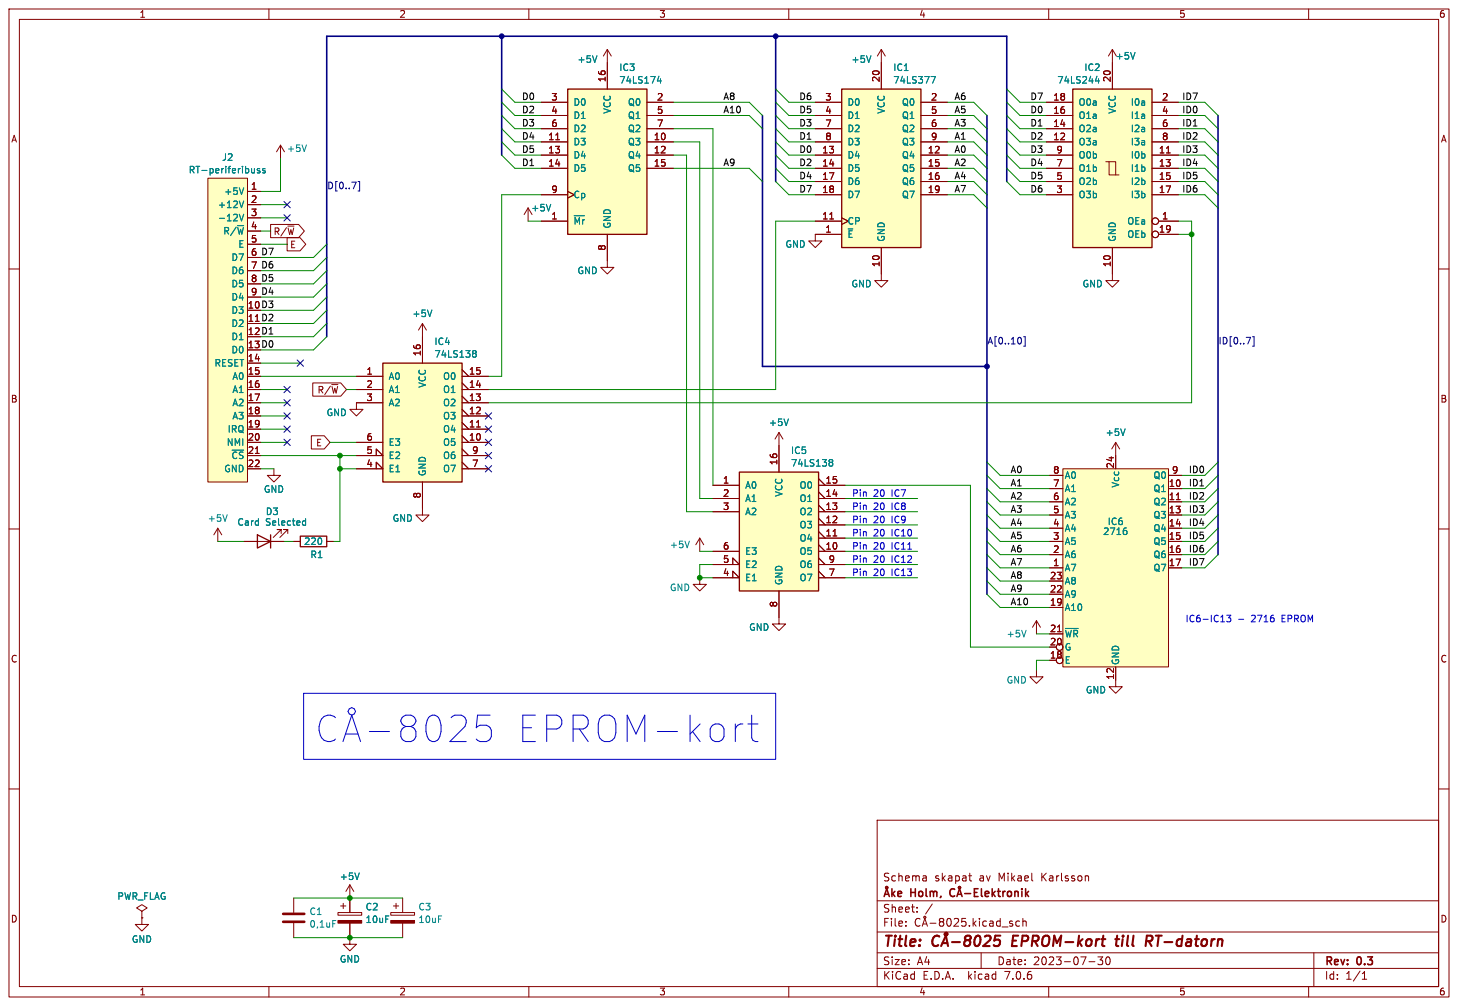
[picture p47: page 1]

Pin 20 IC12 Pin 20 IC13 Pin 20 IC7 Pin 20 IC9 Pin 20 IC10 Pin 20 IC11
