mickecamino/RT-datorn/Gamla RT-datorn/CÅ-8008/CÅ-8008-schema.pdf

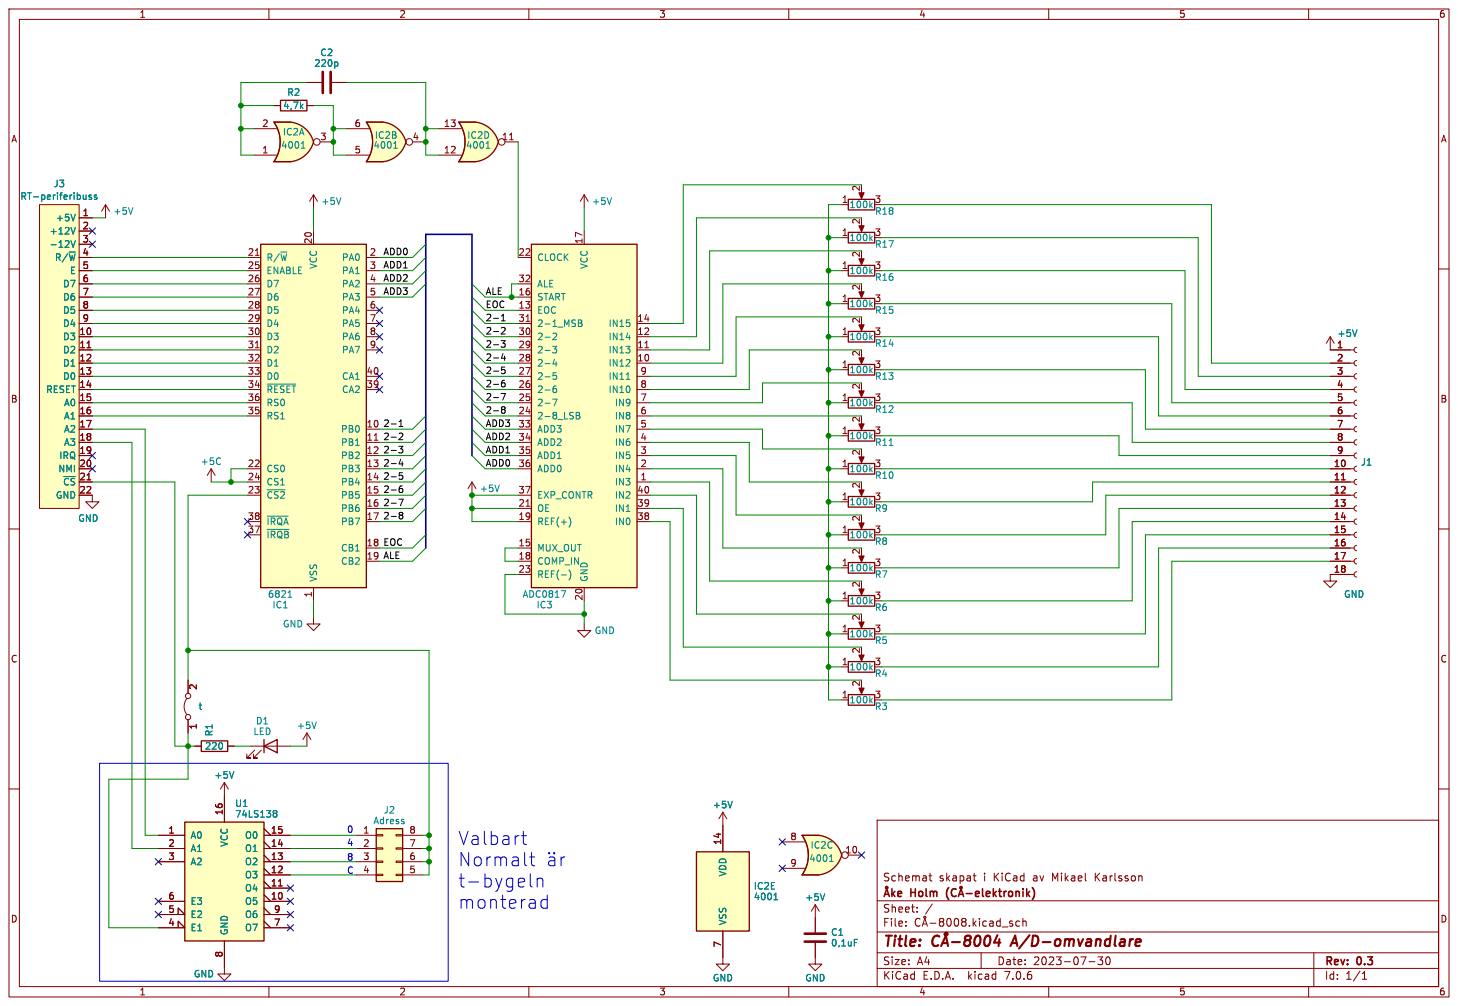
[picture p48: page 1]

4001 VDD 14 VSS 7 +5V GND GND

Id: 1/1 Title: þÿCÅ-8004 A/D-omvandlare
