mickecamino/RT-datorn/Nya RT-datorn/CÅ-836/CÅ-836-schema.pdf

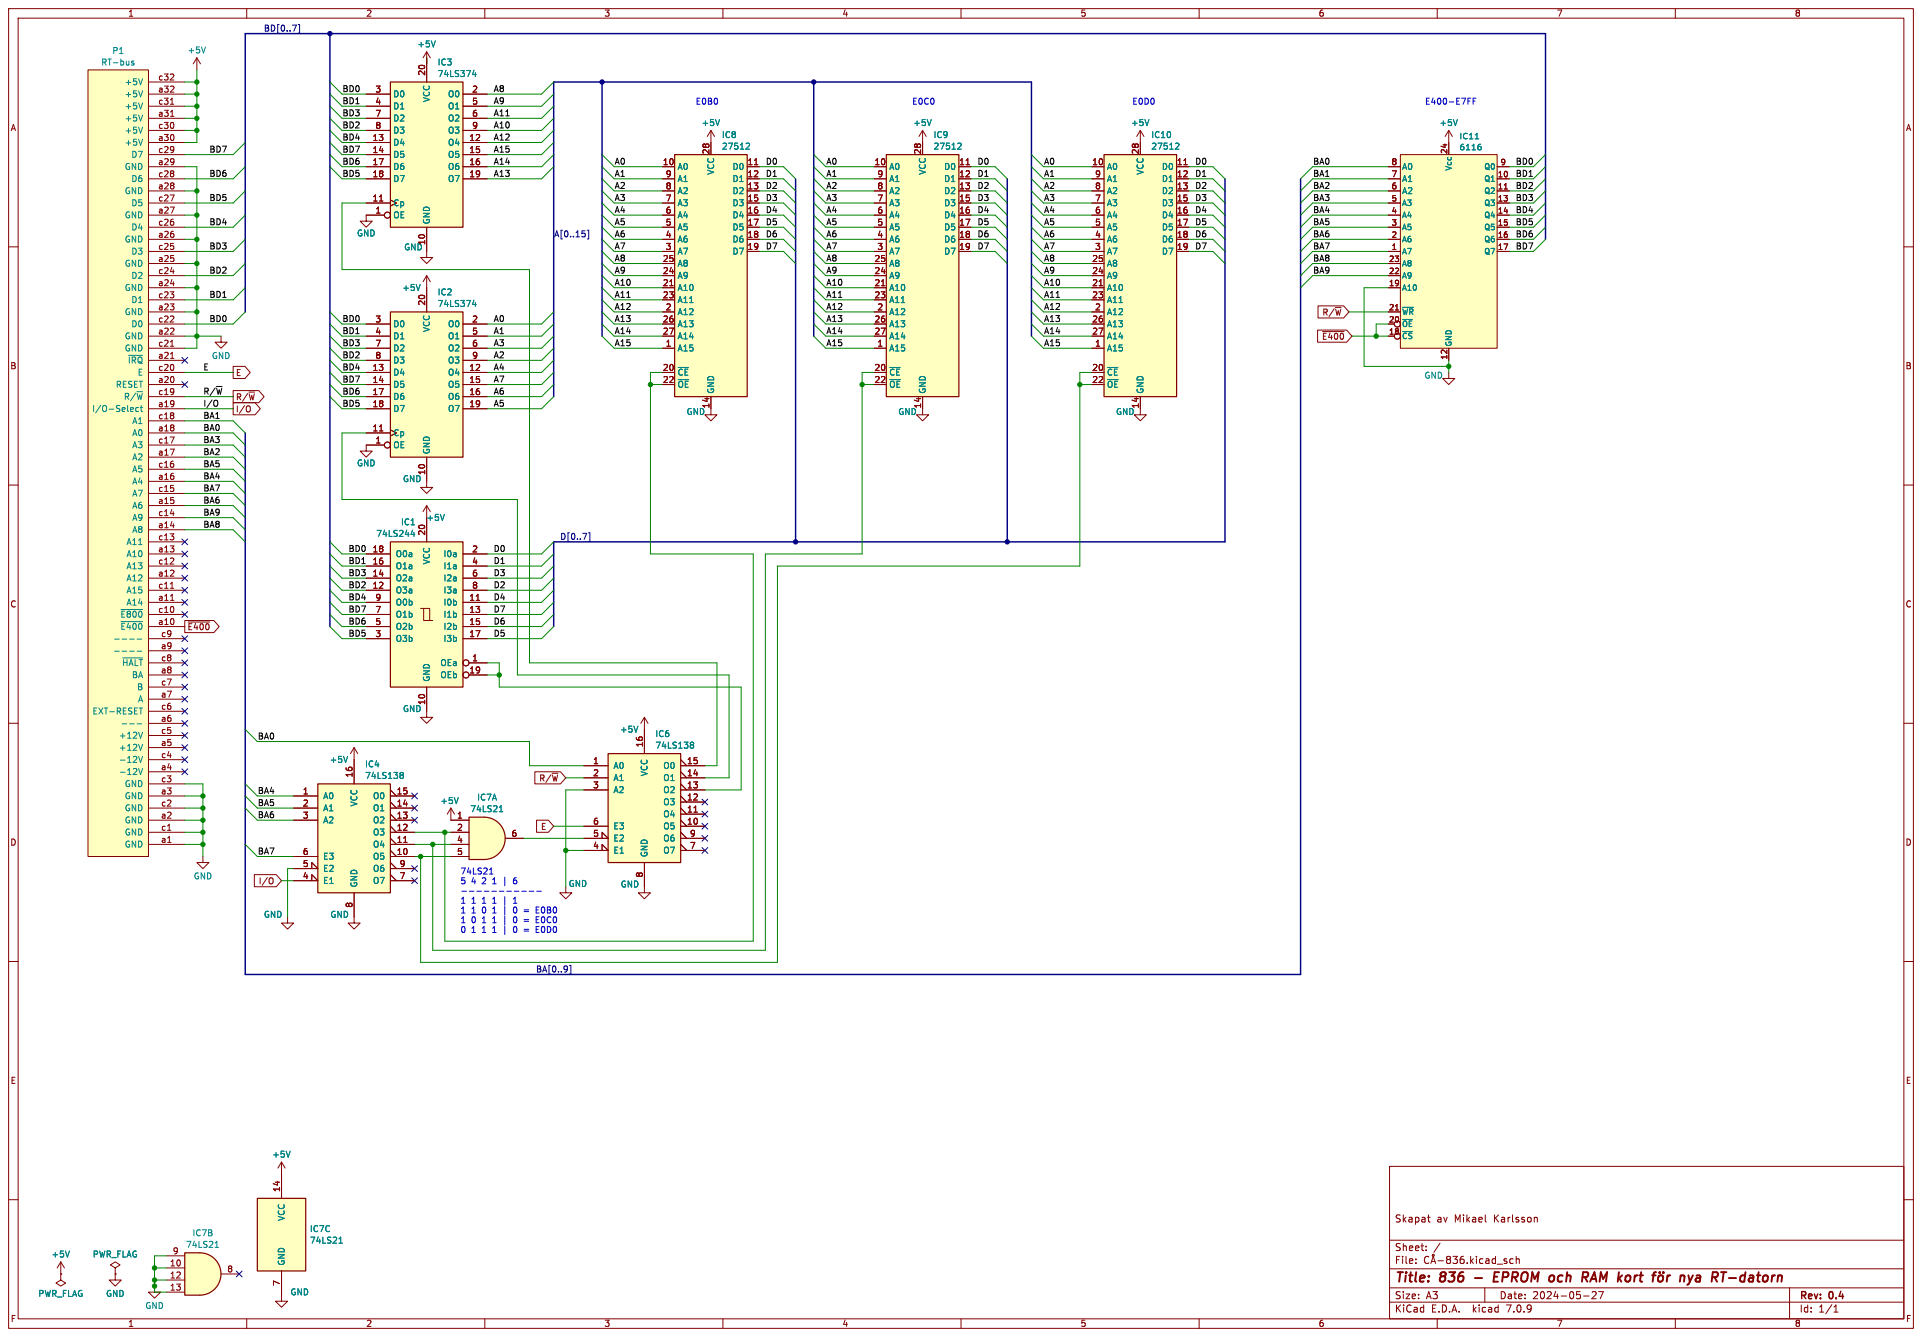
[picture p52: page 1]

Id: 1/1 Title: 836 - EPROM och RAM kort þÿför nya RT-datorn
