mickecamino/RT-datorn/Nya RT-datorn/CÅ-837/CÅ-837-schema.pdf

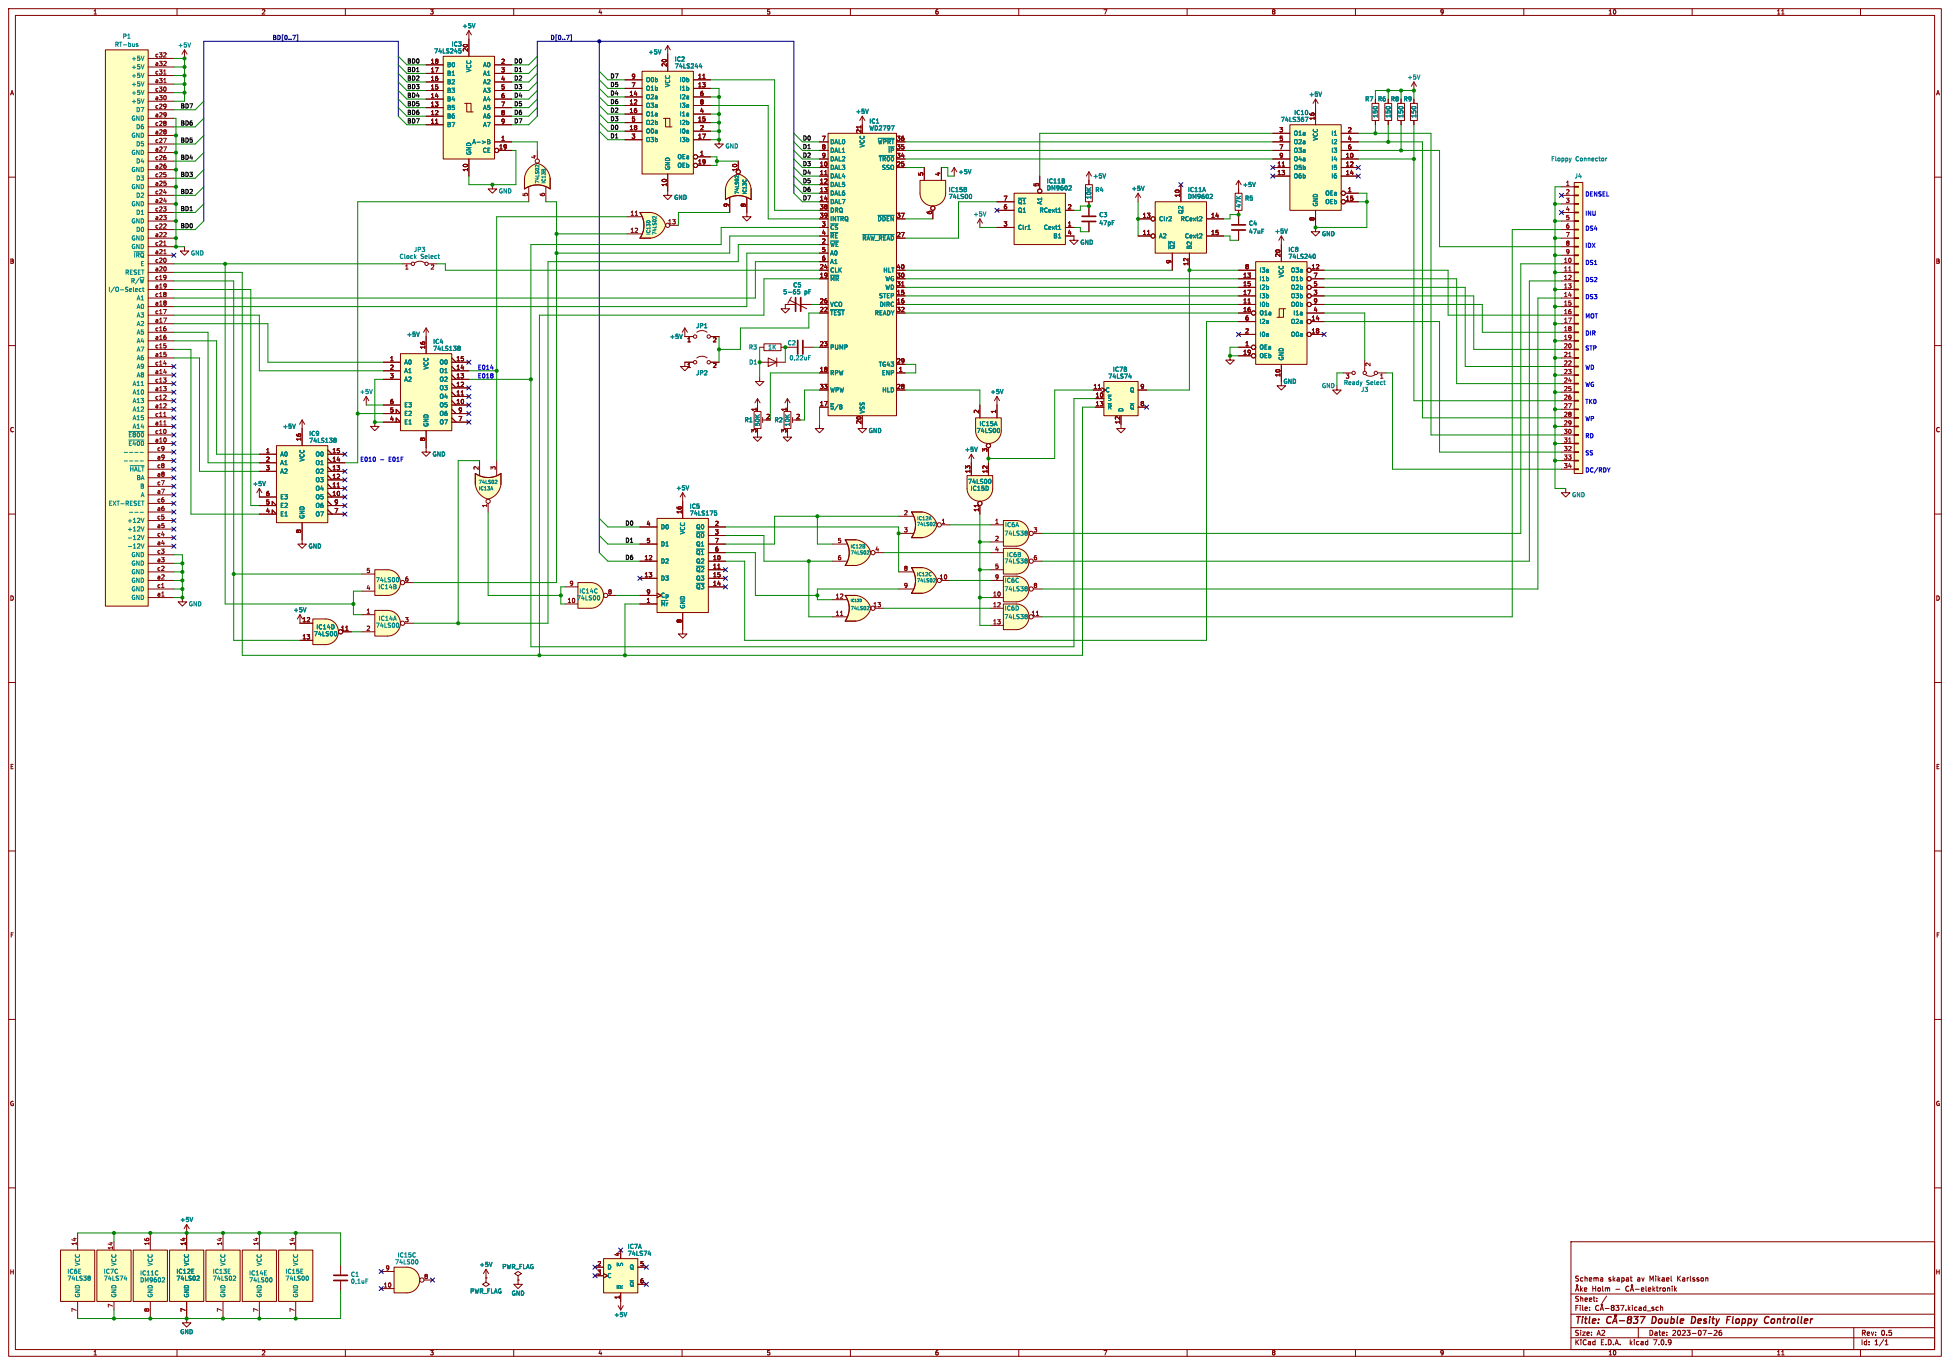
[picture p53: page 1]
