mickecamino/RT-datorn/Gamla RT-datorn/CÅ-8005/CÅ-8005-schema.pdf

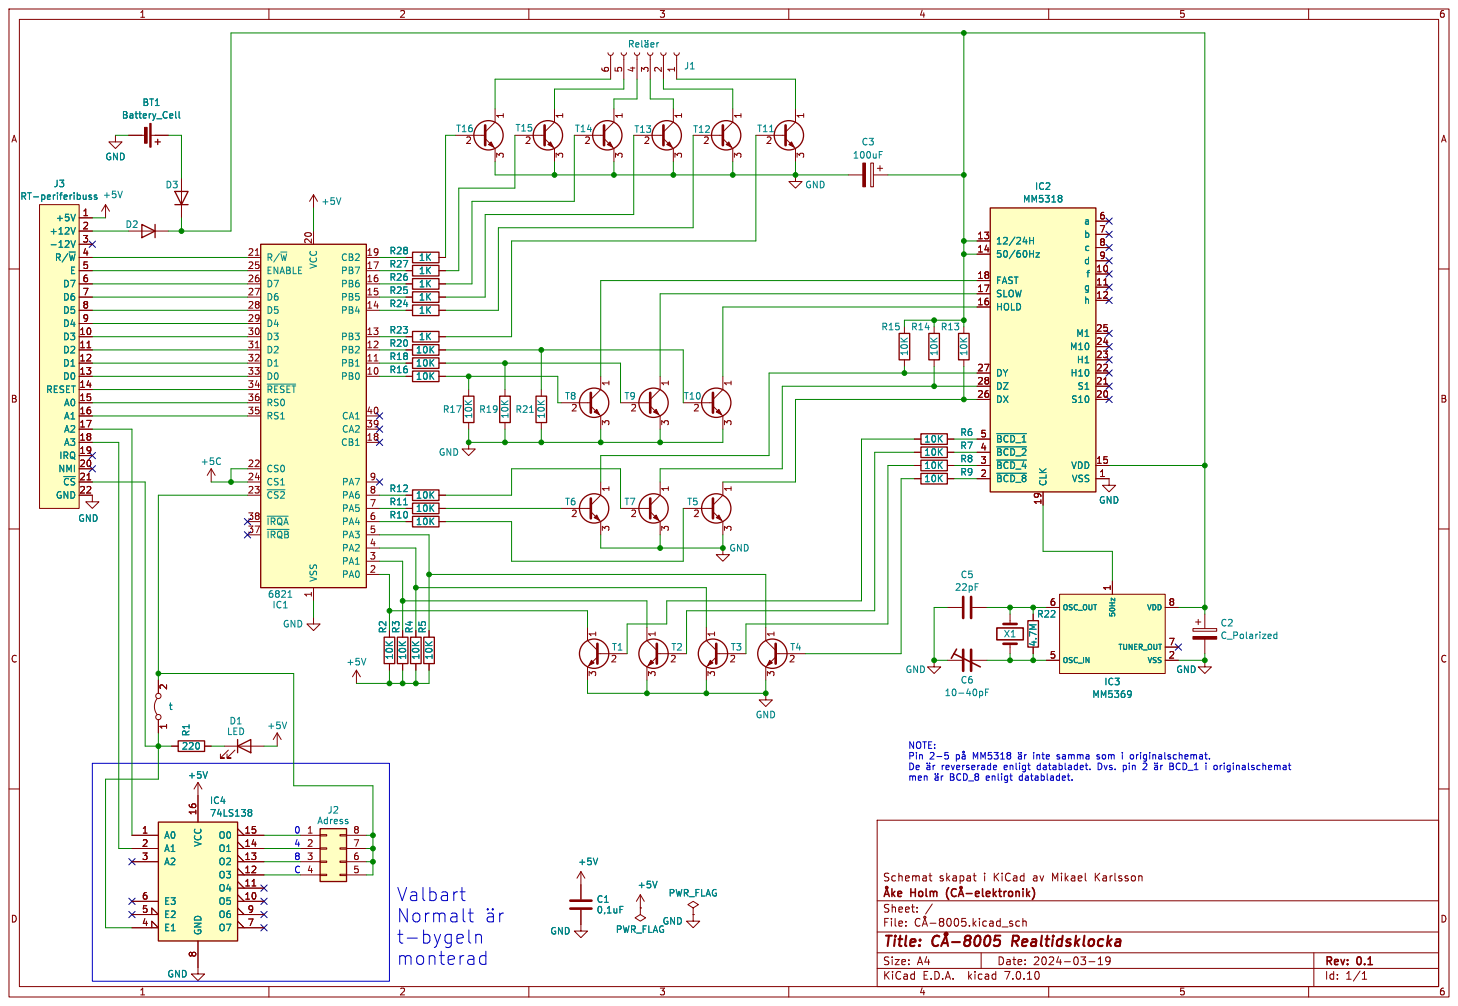
[picture p54: page 1]

Id: 1/1 Title: þÿCÅ-8005 Realtidsklocka
