mickecamino/RT-datorn/Nya RT-datorn/CÅ-837/CÅ-837-PCB.pdf

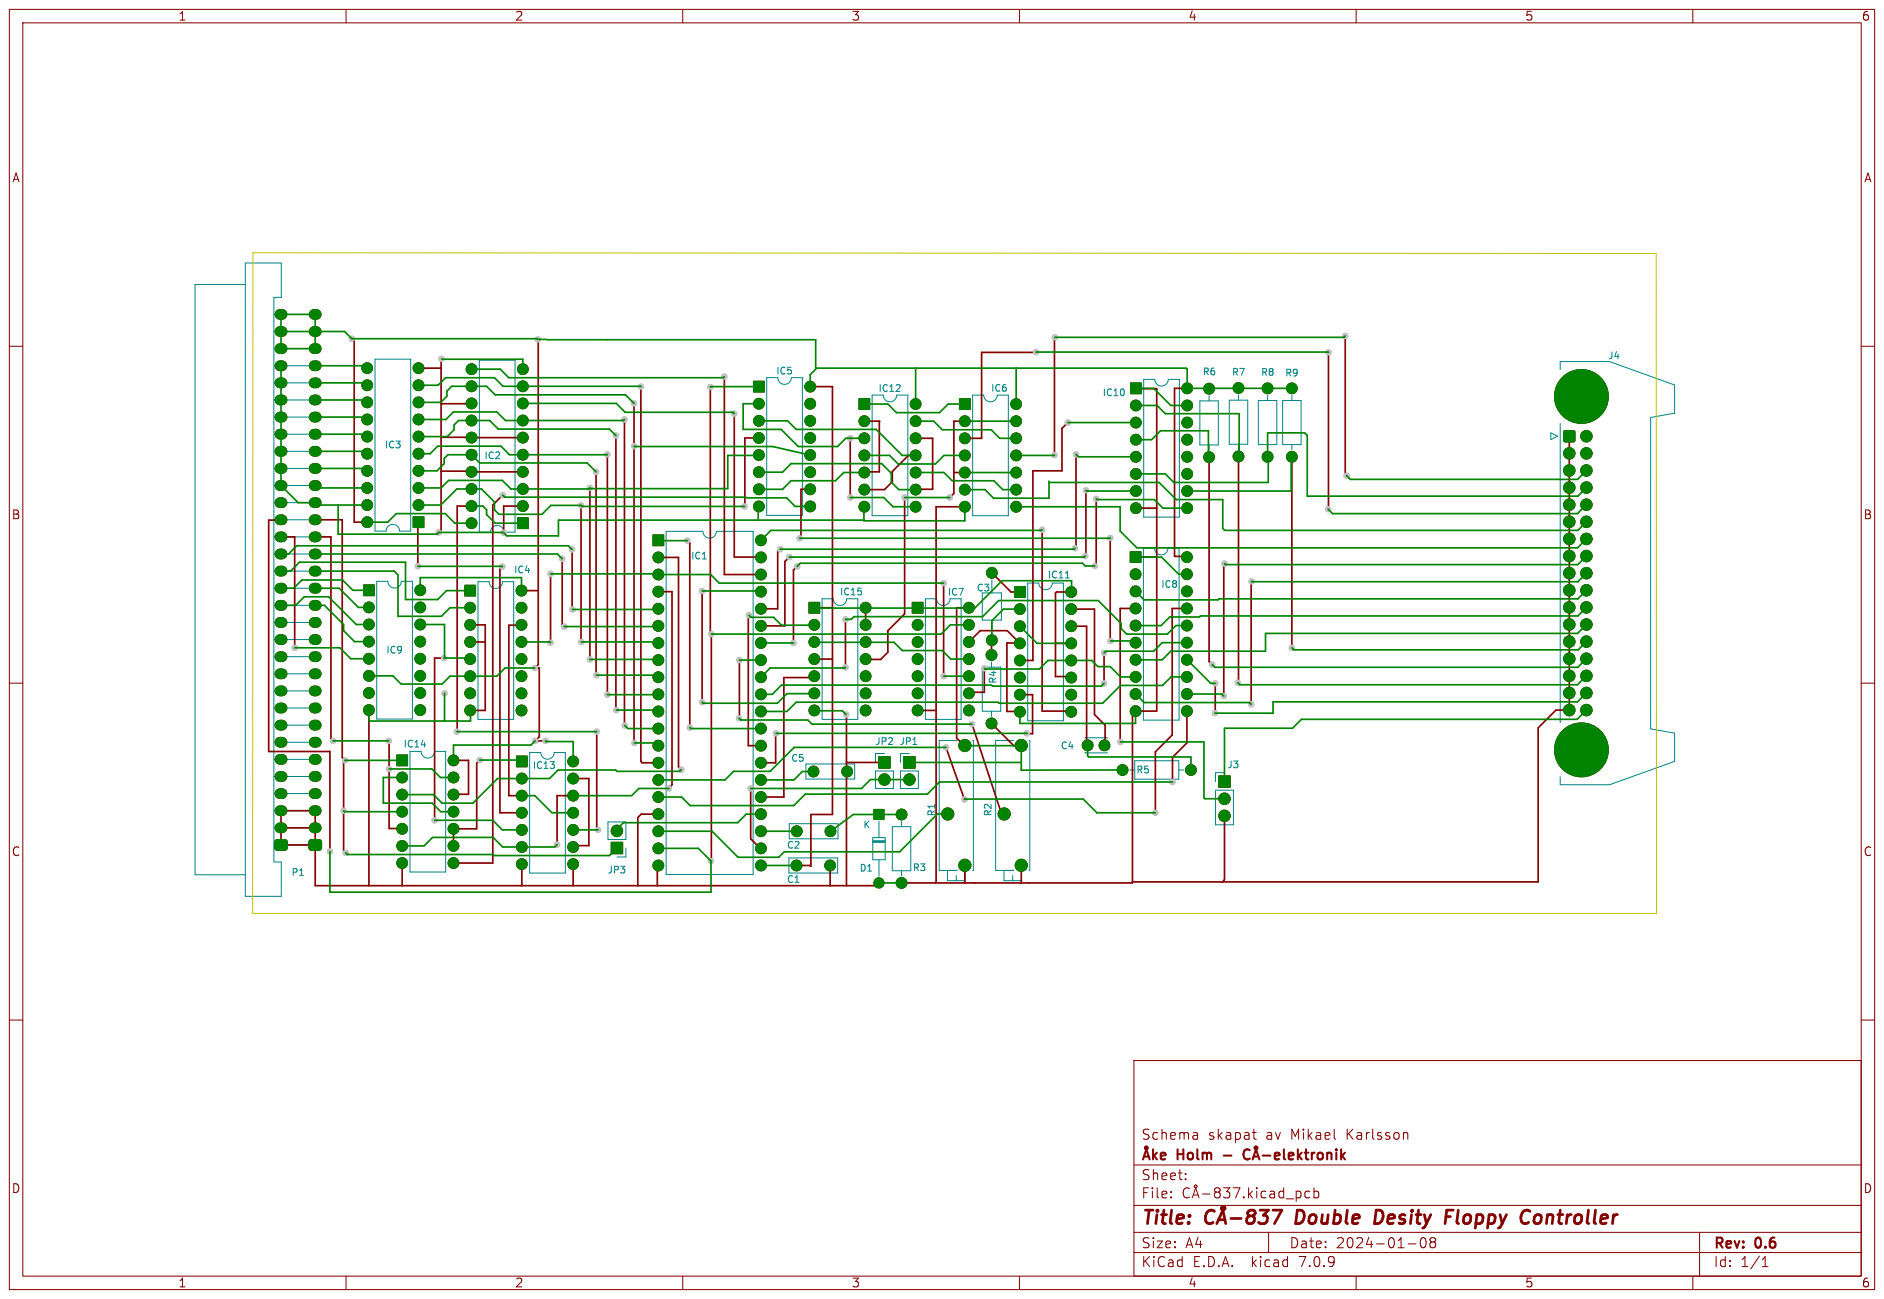
[picture p55: page 1]
