mickecamino/RT-datorn/Nya RT-datorn/CÅ-833/CÅ-833-PCB.pdf

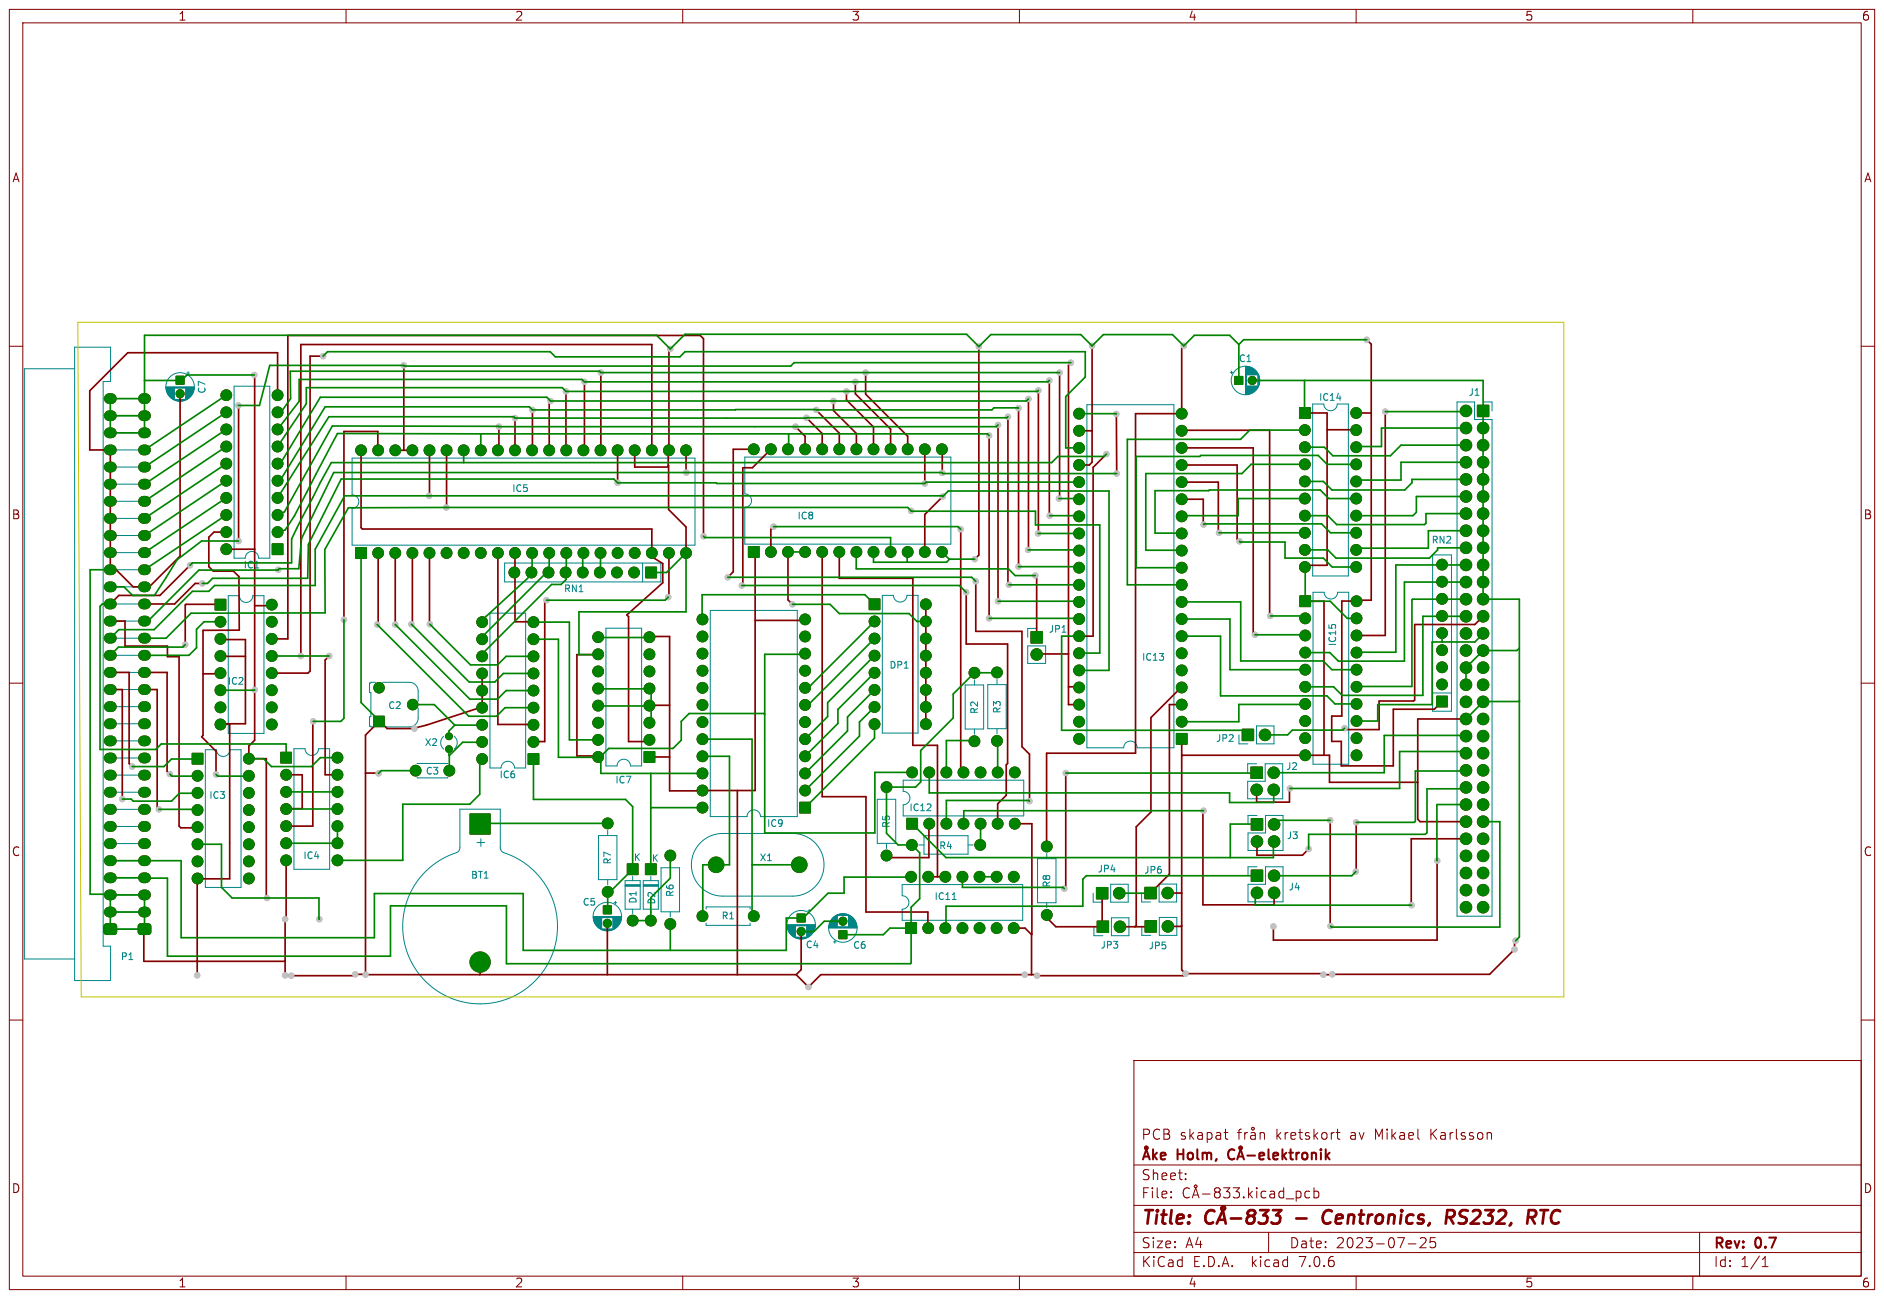
[picture p56: page 1]

Id: 1/1 Title: þÿCÅ-833- Centronics, RS232, RTC
