mickecamino/RT-datorn/Gamla RT-datorn/CÅ-8015/CÅ-8015.pdf

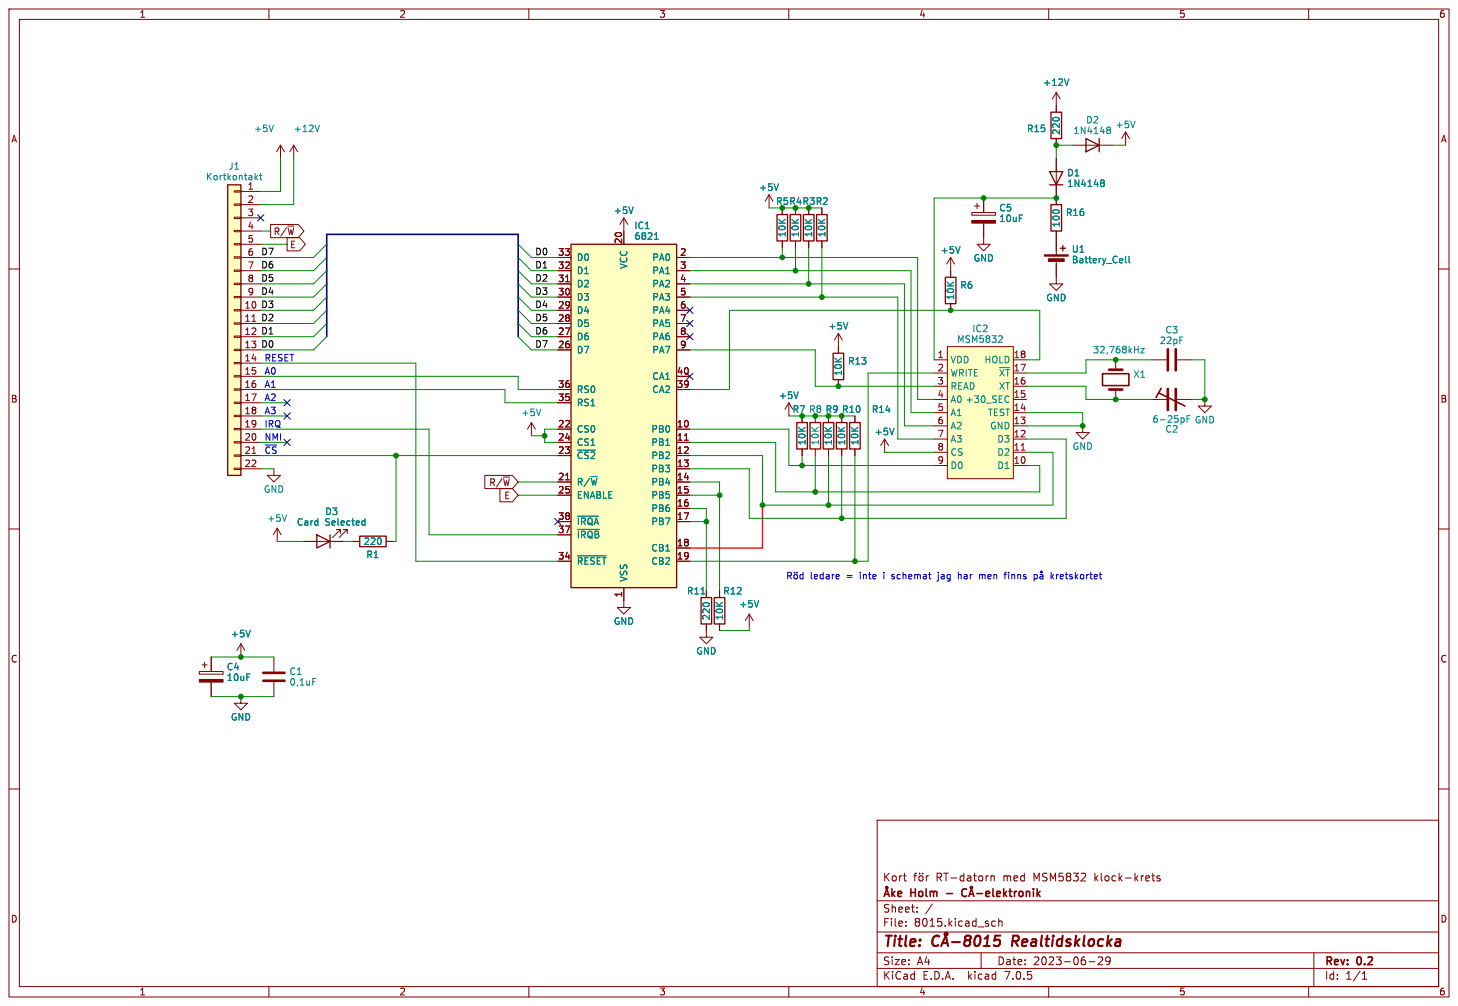
[picture p57: page 1]

Id: 1/1 Title: þÿCÅ-8015 Realtidsklocka
